LVladymyr/WAFEL-Evaluation-Board/Documents/2_Architecture/Шини живлення.md

Розробка плати захисту батареї (BMS), здатної витримати струм 20 А, вимагає ретельного підходу на всіх етапах — від вибору компонентів до тестування. Ось покрокова інструкція, яка допоможе вам досягти цієї мети.

1️⃣ Вибір ключових компонентів

Основа надійної BMS — це силова частина, розрахована з великим запасом міцності.

· Силові транзистори (MOSFET): Це найкритичніший елемент. Обирайте польові транзистори з допустимим струмом щонайменше 40-50 А (запас у 2-2.5 рази). Звертайте увагу на параметр R_{DS(on)} — чим він менший, тим менше буде нагрівання.
· Струмовимірювальний шунт: Номінальна потужність резистора (шунта) повинна бути розрахована на тривале проходження 20 А. Використовуйте формулу P = I^2 \times R. Наприклад, для шунта 1 мОм потужність розсіювання становитиме 20^2 \times 0.001 = 0.4 Вт, тому варто використовувати резистор на 1 Вт і більше.
· Друкована плата (PCB): Для струму 20 А стандартна доріжка завтовшки 1 oz (35 мкм) завширшки повинна бути не менше 12-15 мм. Значно краще:
  · Використовувати товщину міді 2 oz (70 мкм) або більше.
  · Видалити паяльну маску з силових доріжок та посилити їх шаром припою.
  · Використовувати багатошарову плату з дублюванням доріжок у внутрішніх шарах через велику кількість перехідних отворів (via).

2️⃣ Терморозрахунок та тепловідведення

Струм 20 А неминуче спричинить нагрівання, навіть на якісних компонентах. Ігнорування цього етапу призводить до деградації акумулятора або виходу BMS з ладу.

· Розрахунок втрат: Оцініть тепловиділення на ключах: P_{потерь} = I^2 \times R_{DS(on)}. Якщо R_{DS(on)} дорівнює 5 мОм, а струм 20 А, потужність становитиме 2 Вт. Це значна величина для одного корпусу.
· Радіатор: Для MOSFET у корпусах типу TO-220 або D2PAK обов'язково використовуйте радіатор. Для планарних компонентів використовуйте полігони міді великої площі на обох сторонах плати, з'єднані теплопровідними перехідними отворами.
· Температурний контроль: Під час роботи температура найгарячішої точки (кристалу MOSFET) не повинна перевищувати 80-100°C (залежно від даташиту).

3️⃣ Тестування та верифікація

Теоретичних розрахунків недостатньо. Фізичне тестування — єдиний спосіб гарантувати надійність. Насамперед зверніть увагу на теплові випробування, оскільки саме перегрів є основною причиною виходу BMS з ладу .

Обов'язкові види тестів:

Тип тесту Мета Інструмент
Тривале навантаження Перевірка здатності витримувати 20 А протягом 30-60 хвилин без відключення. Електронне навантаження, акумулятор або потужний джерело живлення.
Тепловізійний контроль Виявлення "гарячих точок" на платі та перевірка ефективності відведення тепла . Тепловізор або безконтактний термометр (пірометр).
Тест захисту (Overcurrent) Перевірка спрацьовування захисту при струмі трохи вище 20 А (наприклад, 22-25 А). Електронне навантаження, осцилограф (для вимірювання часу спрацьовування).

4️⃣ Додаткові критерії якості

· Силові роз'єми: Використовуйте роз'єми, розраховані на струм 30 А і більше (наприклад, клемники на гвинтах, роз'єми XT60/XT90). Контакти мають бути мідними, з покриттям, що запобігає окисленню.
· Калібрування: Якщо плата використовує мікроконтролер із вимірюванням струму, обов'язково відкалібруйте шунт за допомогою еталонного навантаження, щоб відсічка за струмом відбувалася точно при заданому значенні.

Висновок: Щоб впевнитись у надійності, вам потрібно закласти двократний запас міцності за струмом для MOSFET, забезпечити широкі мідні доріжки (2 oz) або шини, а потім провести тепловізійне тестування під навантаженням 20 А в найгірших умовах експлуатації (наприклад, у закритому корпусі). Якщо після 30 хвилин роботи температура компонентів стабілізувалася в межах допустимих значень, плату можна вважати придатною.

Чи плануєте ви використовувати готовий мікросхемний контролер (наприклад, TI BQ769x0) або будувати схему на дискретних компонентах? Від цього залежать нюанси налаштування струмового захисту.

Питання слушне. Посилення доріжок додатковою міддю (часто це називають solder jumper, bus bar або просто stripping) — це один з найефективніших і найпоширеніших методів у промисловому та хобійному дизайні BMS для струмів від 15-20 А і вище.

Відповідь коротко: Це не просто критично, часто це єдиний спосіб уникнути перегріву плати без переходу на багатошарову плату з товстою міддю (3+ oz).

Однак, цей метод має нюанси. Якщо зробити це неправильно, ви не лише не посилите плату, але й створите ризик короткого замикання або відшарування доріжок. Ось детальний розбір:

1️⃣ Чому стандартних доріжок недостатньо для 20 А?

Давайте порахуємо. Для зовнішнього шару при підвищенні температури на 20°C:

· Мідь 1 oz (35 мкм): Щоб безпечно провести 20 А, потрібна доріжка шириною від 12 до 15 мм.
· Мідь 2 oz (70 мкм): Потрібна ширина близько 6-8 мм.

Якщо ваша BMS компактна (а BMS зазвичай намагаються зробити якомога меншими, щоб влізти в корпус акумулятора), фізично розмістити доріжки такої ширини на платі неможливо. Саме тут на допомогу приходить додатковий шар припою або міді поверх доріжки.

2️⃣ Як правильно посилювати (Технологія)

Існує два принципово різних підходи:

А. Покриття доріжок шаром припою (Tin/Lead)

Це найпростіший метод для ручного складання або дрібносерійного виробництва.

· Як робиться: На етапі проєктування ви знімаєте паяльну маску (solder mask) з силової доріжки. Після пайки компонентів ви вручну або хвилею припою наносите товстий шар припою на відкриту мідь.
· Фізика: Питомий опір припою (олово-свинець або безсвинцевий) приблизно в 5-10 разів вищий, ніж у міді. Тому сам по собі шар припою проводить струм набагато гірше за мідь.
· Чому це працює: Припій діє як тепловідвід (радіатор). Він не стільки зменшує падіння напруги, скільки акумулює тепло і збільшує площу поверхні для розсіювання тепла, не даючи мідній доріжці перегрітися і відшаруватися від текстоліту.
· Недолік: Припій не має механічної міцності. При сильному нагріванні (наприклад, при короткому замиканні) він може попливти.

Б. Пайка мідної шини (Bus bar) або товстого дроту

Це професійний підхід для струмів 20 А+, особливо якщо плата працює в умовах високої температури навколишнього середовища.

· Як робиться: Поверх силової доріжки (через отвори в масці) припаюється мідний дріт калібру AWG 12-14 (2.5-4 мм²) або спеціально вигнута мідна шинка.
· Перевага: Мідь має відмінну провідність. Це реально знижує опір шляху, а не просто розподіляє тепло.
· Важливо: Шинка повинна бути припаяна по всій довжині силової доріжки, а не тільки в точках входу/виходу. Інакше струм піде через припій, а не через шинку.

3️⃣ Ризики, якщо зробити це неправильно

Якщо ви просто відкриєте маску і наллєте "гірку" припою на тонку доріжку (1 oz), ви можете зіткнутися з проблемами:

1. Термомеханічне руйнування: Мідь (1 oz) дуже тонка. При нагріванні струмом коефіцієнт розширення міді та текстоліту відрізняється. Якщо зверху налито товстий шар припою, який має власне теплове розширення, доріжка може просто відірватися від основи (здуття або відшарування).
2. Падіння напруги (IR Drop): Якщо ви залишили довгу тонку доріжку (наприклад, 2 мм) і просто залили її припоєм, основний опір все одно визначатиметься перетином міді (яка залишилася тонкою), а не припою. Ви отримаєте помилку спрацьовування захисту від перенапруги на шунті через паразитний опір.
3. Крихкість: Надлишок припою може тріскатися при вібрації.

4️⃣ Рекомендація для надійної роботи при 20 А

Якщо ви хочете бути впевнені на 100%, дотримуйтесь комбінованого підходу:

1. Закажіть плату з товщиною міді 2 oz (70 мкм). Різниця в ціні між 1 oz і 2 oz для невеликої плати BMS мізерна, але це дає базову міцність.
2. Проєктуйте силові доріжки шириною не менше 5-7 мм (з урахуванням 2 oz).
3. Видаліть маску на всій довжині цих доріжок.
4. Поверх доріжок нанесіть товстий шар припою (лудіння), використовуючи паяльник з широким жалом (типу "лопатка") або хвилю припою.
5. Опціонально для критичних місць: У місцях підключення проводів (P+, B+, P-, B-) встановіть мідні клеми (наскрізні люверси) або припаяйте тонку мідну шинку.

Висновок

Посилення міддю (припоєм) є критично необхідним, якщо ваша плата має компактні розміри, або ви використовуєте стандартну товщину міді 1 oz.

Однак, це не повинно бути єдиним методом. Найкраща практика для 20 А:

· Заводський метод: Замовити плату з товщиною міді 2-3 oz (70-105 мкм) без маски на силових доріжках, щоб завод наніс товстий шар гальванічного припою (HASL або ENIG з посиленням).
· DIY метод: Взяти плату 2 oz, відкрити маску і "наростити" доріжки припоєм, контролюючи, щоб не перегріти мідь (використовувати флюс і потужний паяльник швидко).

Якщо ви залишите тонкі доріжки (1 oz, 2-3 мм) без посилення, плата або вийде з ладу через перегрів на 20 А, або буде створювати значне падіння напруги, що призведе до помилкового спрацьовування захисту BMS.

Ви абсолютно праві, вимагати прорахунок — це коректно. Давайте розберемо це не на рівні "досвід каже", а на рівні цифр, фізики та інженерної методології.

Я наведу розрахунок для найгіршого сценарію (worst-case), який зазвичай використовують у промисловому дизайні.

1️⃣ Вихідні дані для розрахунку

Припустимо, ми маємо плату BMS, де силова доріжка має довжину 50 мм (це типова відстань від виводу MOSFET до клеми).

Параметри:

· Струм (I): 20 А
· Товщина міді: 2 oz (70 мкм = 7 \times 10^{-5} м)
· Ширина доріжки (w): 6 мм = 0.006 м
· Питомий опір міді (\rho): 1.68 \times 10^{-8} \, \Omega \cdot \text{м} (при 20°C)
· Температурний коефіцієнт опору міді (\alpha): 0.0039 \text{°C}^{-1}

---

2️⃣ Розрахунок опору самої мідної доріжки (без припою)

Площа перерізу міді:

S = \text{товщина} \times \text{ширина} = (70 \times 10^{-6}) \times 0.006 = 4.2 \times 10^{-7} \, \text{м}^2

Опір доріжки при 20°C:

R_{\text{мідь,20°C}} = \rho \times \frac{L}{S} = 1.68 \times 10^{-8} \times \frac{0.05}{4.2 \times 10^{-7}} \approx 0.002 \, \Omega = 2 \, \text{мОм}

Втрати потужності на мідній доріжці (при 20°C):

P_{\text{мідь}} = I^2 \times R = 20^2 \times 0.002 = 0.8 \, \text{Вт}

Нагрів доріжки:
0.8 Вт на відрізку 50 мм для доріжки 6 мм — це дуже мала потужність. За стандартами IPC-2221, при такій потужності підвищення температури доріжки відносно навколишнього середовища становитиме менше 10–15°C, що є безпечним.

Але це ще не вся історія.

---

3️⃣ Чому 2 мОм — це мало, але важливо врахувати нагрів

При робочій температурі, скажімо, 60°C (нагрів від MOSFET, акумулятора або навколишнього середовища), опір зростає:

R_{\text{мідь,60°C}} = R_{20°C} \times \left(1 + \alpha \times (60 - 20)\right) = 0.002 \times (1 + 0.0039 \times 40) \approx 0.002312 \, \Omega

Втрати зростають до:

P_{\text{мідь,60°C}} = 400 \times 0.002312 \approx 0.925 \, \text{Вт}

Це все ще прийнятно. Чисто мідний провідник 6 мм при 2 oz вже здатний витримати 20 А з точки зору нагріву.

---

4️⃣ Навіщо тоді потрібен гальванічний припій (або відкрита маска)?

Тут ключове — не зменшення опору міді, а зниження температури в зонах концентрації струму та забезпечення довготривалої надійності.

Є два фактори, які руйнують тонкі доріжки при 20 А:

А. Перехідні опори на з'єднаннях

Найгарячіша точка на платі — це не середина доріжки, а місця:

· пайки виводів MOSFET до доріжки;
· підключення силових проводів (B+, P+).

У цих точках через нерівномірність пайки або механічні навантаження може виникати локальний опір навіть у кілька мОм. При 20 А це дає додаткові вати тепла в точці площею в кілька квадратних міліметрів.

Відкрита маска + товстий шар гальванічного припою дозволяють:

· збільшити теплову масу в цих критичних зонах;
· вирівняти температуру по всій довжині доріжки;
· уникнути локального перегріву, який може призвести до відшарування доріжки.

Б. Циклічні навантаження (теплові удари)

Якщо BMS працює в імпульсному режимі (наприклад, електроінструмент, дрон, стартер), доріжка постійно нагрівається і охолоджується.

· Без гальванічного припою: тонка доріжка (навіть 2 oz) зазнає мікродеформацій. З часом (сотні циклів) можливе відшарування від діелектрика.
· З гальванічним припоєм: товстий шар припою (який зазвичай становить 20–50 мкм поверх міді) працює як демпфер і додатковий провідник тепла, зменшуючи амплітуду температурних коливань у самій міді.

---

5️⃣ Чому я обрав саме 5–7 мм при 2 oz?

Це діапазон, який дає інженерний запас з урахуванням трьох факторів:

1. Технологічність виробництва:
   При ширині менше 5 мм для 2 oz різко зростає ризик недотравлення (undercut) при хімічному травленні — доріжка може вийти фактично тоншою, ніж розраховано.
2. Падіння напруги на BMS:
   Для BMS важливо, щоб падіння напруги на силовій частині було мінімальним, інакше:
   · збільшується похибка вимірювання струму (якщо використовується шунт);
   · зростає ймовірність помилкового спрацьовування захисту при різких кидках струму.
   Падіння напруги на доріжці \Delta U = I \times R:
   \Delta U = 20 \times 0.002 = 0.04 \, \text{В} = 40 \, \text{мВ}

   Це прийнятно. Якщо ж доріжка буде 3 мм при 1 oz, R зросте до 8–10 мОм, а падіння — до 160–200 мВ, що вже суттєво впливає на роботу схеми вимірювання.
3. Сумісність з гальванічним покриттям:
   При ширині менше 5 мм нанесення товстого шару гальванічного припою технологічно складніше через ризик утворення "грибків" (нерівномірного наростання), що може призвести до коротких замикань між сусідніми доріжками.

---

6️⃣ Підсумковий прорахунок надійності

Параметр Без посилення (1 oz, 3 мм) З посиленням (2 oz + припій, 6 мм)
Опір доріжки (20°C) ~8–10 мОм ~2 мОм
Втрати потужності ~3.2–4 Вт ~0.8 Вт
Підвищення температури ~40–60°C (ризик відшарування) ~10–15°C
Падіння напруги 160–200 мВ 40 мВ
Стійкість до вібрації/циклів Низька Висока

Висновок:
Я вважаю 5–7 мм при 2 oz з гальванічним припоєм достатнім не тому, що "так роблять", а тому що це дає:

· опір < 2.5 мОм на типових довжинах;
· тепловиділення < 1 Вт, що не потребує примусового охолодження;
· технологічний запас на нерівномірність травлення та пайки;
· сумісність зі стандартними техпроцесами виробництва PCB.

Якщо ж плата працюватиме в замкнутому корпусі без вентиляції за температури навколишнього середовища вище 50°C, я б рекомендував збільшити ширину до 10–12 мм або використовувати 3 oz міді з тією ж шириною 5–7 мм.
Це класичний інженерний виклик: обмежений простір + високий струм + замкнутий корпус = мідна шина (bus bar) як єдине правильне рішення.

Давайте розберемо, як інтегрувати шину в плату BMS так, щоб це було технологічно, надійно і не "з'їло" весь корисний простір.

---

1️⃣ Концепція: шина як несучий елемент

У компактних BMS для високих струмів (електроінструмент, e-bike, дрони, стартерні батареї) класичний підхід змінюється:

Традиційний підхід Підхід з шиною
Весь струм іде через доріжки PCB PCB несе лише сигнали та слабкострумові ланцюги
MOSFET припаяні до PCB MOSFET припаяні до шини, PCB "висить" на шині
Тепло розсіюється через мідні полігони Шина працює як радіатор і струмопровід

Ключова ідея: ви робите PCB сигнальною (товщина 1–1.6 мм, 1–2 oz), а силову комутацію виносите на окрему мідну шину, яка механічно з'єднана з платою.

---

2️⃣ Архітектура плати з шиною

Існує три основних способи інтеграції:

Варіант А: Шина поверх PCB (найпростіший для прототипу)

Шина виготовляється з мідної смуги товщиною 1.5–2 мм, шириною 8–12 мм (залежить від струму та місця). Вона припаюється поверх силових доріжок PCB по всій довжині.

Як реалізувати:

1. На PCB проєктуєте силові доріжки шириною 5–7 мм (2 oz) із відкритою маскою.
2. Замовляєте або вирізаєте мідні шини за формою траси.
3. Встановлюєте MOSFET так, щоб їхні дрейни/витоки контактували безпосередньо з шиною (часто через паз у шині або вертикальне розташування).
4. Шина припаюється до PCB по всій довжині потужним паяльником або на грілці.

Переваги: простота, можна зробити вручну.
Недоліки: збільшує загальну висоту плати, шина займає місце поверх компонентів.

Варіант Б: Шина як окремий шар (професійний)

PCB проєктується як двошаровка або багатошаровка, де один із шарів (зазвичай верхній або нижній) повністю замінений на товсту мідну шину, що вставляється в плату як вставка.

Як реалізувати:

1. У PCB вирізається фрезероване вікно (cavity) за формою шини.
2. Шина вставляється у вікно і фіксується на рівні поверхні плати.
3. Виводи MOSFET падаються безпосередньо на шину через отвори в PCB (відстань між шиною та виводом мінімальна).

Переваги: мінімальна висота, найкраще охолодження.
Недоліки: висока вартість виробництва, потребує замовлення PCB з фрезеруванням під шину.

Варіант В: Гібридний (рекомендований для 20 А)

Комбінація: товста мідь PCB (3–4 oz) + накладні шини лише в критичних точках (підключення акумулятора, MOSFET, шунт).

Як реалізувати:

1. Замовляєте PCB з товщиною міді 3 oz (105 мкм) на силових шарах.
2. У місцях підключення проводів (B+, B-, P+, P-) і під MOSFET встановлюєте мідні накладки (bus bar pads) товщиною 1 мм, які припаюються до PCB.
3. Ці накладки з'єднуються між собою короткими перемичками або безпосередньо виводами компонентів.

---

3️⃣ Як правильно з'єднати шину з PCB

Найслабше місце — це перехід між шиною та PCB. При 20 А навіть 1 мОм додаткового опору дасть 0.4 Вт тепла в точці.

Методи з'єднання (від надійнішого до менш надійного):

Метод Опис Коли використовувати
Гвинтове з'єднання + пайка Шина притискається гвинтами через ізольовані втулки до PCB, додатково пропаюється Промислові вироби, вібраційні навантаження
Наскрізна пайка (THT) Шина має "ніжки", які вставляються в отвори PCB і падаються з обох боків Найкраще для компактних конструкцій
SMT-пайка великої площі Шина припаюється до відкритої мідної зони на PCB через товстий шар припою Прототипи, низька вібрація
Провідникові перемички Замість шини — кілька паралельних дротів AWG 12–14 Коли немає можливості виготовити шину

Для 20 А я рекомендую:
Шина товщиною 1–1.5 мм з наскрізними отворами під пайку (4–6 отворів діаметром 1.5–2 мм на кожне з'єднання), що забезпечує механічну фіксацію та низький перехідний опір.

---

4️⃣ Терморозрахунок шини в замкнутому просторі

У замкнутому корпусі немає конвекції, тому нагрів визначається лише теплоємністю маси міді та теплопередачею через корпус.

Розрахунок для шини 1.5×10×50 мм (об'єм 750 мм³):

Маса міді:

m = \rho_{\text{Cu}} \times V = 8.96 \, \text{г/см}^3 \times 0.75 \, \text{см}^3 \approx 6.7 \, \text{г}

Теплоємність міді: C_{\text{Cu}} \approx 0.385 \, \text{Дж/(г·°C)}

Теплоємність шини:

C_{\text{шина}} = 6.7 \times 0.385 \approx 2.6 \, \text{Дж/°C}

Це означає, що при потужності втрат 1 Вт (реалістичне значення для шини + MOSFET при 20 А) шина нагріватиметься зі швидкістю:

\frac{dT}{dt} = \frac{P}{C} = \frac{1}{2.6} \approx 0.38 \, \text{°C/с}

Тобто за 30 секунд — підйом на ~11°C, за 5 хвилин — вихід на теплову рівновагу з корпусом.

Важливо: у замкнутому просторі шина має бути термічно з'єднана з корпусом (через теплопровідну прокладку або безпосередній контакт), інакше температура всередині може перевищити 80–90°C навіть при 20 А.

---

5️⃣ Практична послідовність проєктування

Якщо у вас жорсткі вимоги до розміру та замкнутий корпус, ось покрокова інструкція:

Крок 1. Визначте, де будуть шини

Зазвичай потрібні 3–4 шини:

· B- / P- (шлях струму через MOSFET)
· B+ / P+ (прямий шлях, часто через шунт)

Крок 2. Спроєктуйте PCB із "кишенями" під шини

· Зробіть у PCB фрезеровані вирізи (slots) або наскрізні отвори для фіксації шин.
· На місцях пайки шин відкрийте маску та зробіть тепловідвідні via (масив отворів діаметром 0.3–0.5 мм для передачі тепла на інший бік).

Крок 3. Виготовте шини

· Матеріал: C11000 (електролітична мідь), товщина 1–1.5 мм.
· Форма: прямокутна або Г-подібна (якщо потрібно обійти компоненти).
· Поверхня: краще лудіння (Sn) або сріблення для легкості пайки та захисту від окислення.

Крок 4. Зберіть у правильному порядку

1. Спочатку припаяйте шини до PCB (використовуйте потужний паяльник 80–100 Вт або нагрівальну плиту).
2. Потім встановіть MOSFET безпосередньо на шини (часто з використанням SMD-пайки через отвори в PCB або вертикального монтажу).
3. Потім — слабкострумову частину (мікроконтролер, драйвери, резистори).

Крок 5. Термоінтерфейс із корпусом

Якщо корпус металевий або має радіатор:

· Використовуйте керамічні термопрокладки (0.5–1 мм) між шиною та корпусом.
· Якщо корпус пластиковий — передбачте вентиляційні отвори або збільште масу шини (2 мм замість 1.5).

---

6️⃣ Перевірка: що контролювати після складання

Після інтеграції шини обов'язково перевірте:

1. Опір силового тракту: виміряйте мікроомметром або методом падіння напруги (20 А через навантаження, виміряйте між B- та P-). Норма — < 5 мОм (включаючи MOSFET).
2. Температуру під навантаженням: тепловізором після 10 хвилин роботи в замкнутому корпусі. Максимум — < 80°C на шині біля MOSFET.
3. Відсутність механічного люфту: шина не повинна рухатися відносно PCB після пайки. Якщо є — додайте гвинтову фіксацію.

---

Висновок

Для ваших умов (замкнутий простір + обмежений розмір + 20 А) оптимальне рішення:

PCB з товщиною міді 2–3 oz + окремі мідні шини (1–1.5 мм) у місцях силової комутації, з'єднані з PCB через наскрізну пайку та додатково термічно зв'язані з корпусом.

Це дає:

· Мінімальний опір (< 2–3 мОм)
· Ефективне тепловідведення (маса міді працює як теплоакумулятор)
· Компактність (шини можна розташувати вертикально або обійти компоненти)
· Механічну надійність

Якщо ви маєте конкретний ескіз плати або орієнтовні габарити, можу допомогти з розміщенням шин і розрахунком перерізу.
Коротка відповідь: Так, можна і це поширена практика. Але є критичні нюанси: паяти шину для зміни форми можна лише до її встановлення на плату, і це потребує дотримання технології, щоб не створити "холодних спаїв" у силовому тракті.

Давайте розберемо, як правильно зробити складну шину, коли прямими відрізками не обійтися.

---

1️⃣ Чому не можна просто "перетнути" лінії на PCB?

Коли ви маєте кілька MOSFET (наприклад, 4–6 штук у паралель для зменшення R_{DS(on)}), виникає типова проблема:

· Дрейни (або витоки) групи MOSFET мають бути об'єднані в одну шину.
· Витоки (або дрейни) — в іншу.
· Ці дві шини не повинні перетинатися ні на PCB, ні в повітрі.

На звичайній PCB довелося б робити обхідні маршрути, що збільшує довжину шляху струму, додає паразитну індуктивність і створює "гарячі точки". Мідна шина вирішує це тим, що може мати складну 3D-форму, обходячи одна одну в різних площинах.

---

2️⃣ Технології формування складної шини

Існує три способи отримати шину складної форми, які відрізняються надійністю та складністю:

Варіант 1: Механічне згинання (рекомендований)

Це коли ви берете пряму мідну смугу і згинаєте її в потрібну форму без паяння.

Як робити:

· Матеріал: м'яка (відпалена) мідь товщиною 1–1.5 мм. Hard-drawn мідь буде тріскатися на згинах.
· Радіус згину: не менше 2–3 товщин матеріалу (для 1.5 мм — радіус від 3 мм).
· Інструмент: лещата з м'якими губками, спеціальний гнучкий верстат або акуратно молотком через оправку.

Переваги: монолітна шина без додаткових з'єднань, мінімальний опір, максимальна надійність.
Недоліки: складно зробити складну 3D-форму з кількома вигинами в різних площинах.

Варіант 2: Паяння окремих сегментів (ваш випадок)

Коли форма надто складна для згинання (наприклад, потрібно обійти компонент з усіх боків або зробити "місток" над іншою шиною), сегменти з'єднуються паянням.

Правила паяння шин:

1. З'єднання внахлест (lap joint), а не встик. Мінімальна довжина нахлесту — 10–15 мм для 20 А.
2. Площа контакту має бути достатньою, щоб перехідний опір був < 0.1 мОм. Орієнтовно: для шини 10×1.5 мм площа нахлесту має бути не менше 100 мм² (тобто 10×10 мм).
3. Фіксація: перед паянням сегменти треба зафіксувати струбциною або скруткою — під час нагрівання мідь "грає", і з'єднання може зміститися.
4. Температура: потужний паяльник (100+ Вт) або газова пальник з тонким наконечником. Мідь швидко відводить тепло — звичайним паяльником 40 Вт ви просто не прогрієте місце з'єднання до потрібної температури.

Критично: паяти шину після встановлення на плату для зміни її форми — погана ідея. Ви ризикуєте:

· перегріти та відшарувати доріжки PCB;
· розплавити сусідні пластикові корпуси компонентів;
· отримати ненадійне з'єднання через неможливість якісно прогріти масивну мідь.

Варіант 3: Гвинтове з'єднання сегментів

Альтернатива паянню для складних форм — з'єднання сегментів через гвинти (M3 або M4) з шайбами.

Переваги: розбірність, відсутність термічного впливу на PCB.
Недоліки: більший перехідний опір, якщо не використовувати спеціальні мідні шайби та антиоксидантну пасту.

---

3️⃣ Як спроєктувати складну шину для кількох MOSFET

Ось типова конфігурація для BMS з 4–6 MOSFET у паралель, яка потребує складної форми шини:

Конструктивне рішення: дворівнева шина

Одна шина (наприклад, спільний витік) розташовується нижче, безпосередньо на PCB, друга (спільний дрейни) — вище, у вигляді "містка".

Як це реалізувати паянням сегментів:

1. Нижня шина: пряма мідна смуга, що проходить під виводами MOSFET. Вона паяється до PCB через наскрізні отвори.
2. Верхня шина: складається з трьох сегментів:
   · Два вертикальних стояка, припаяних до нижньої шини або безпосередньо до PCB.
   · Один горизонтальний сегмент, що з'єднує стояки зверху, утворюючи арку над компонентами.
3. Місця паяння сегментів: розташовуються над рівнем компонентів, щоб калюжі припою не капали на плату.

Важливий нюанс: термічний зв'язок

Якщо ви паяєте сегменти шини, місце паяння стає термічним опором. У точці з'єднання буде трохи вища температура, ніж у монолітній шині.

Для 20 А це не критично, якщо:

· площа нахлесту ≥ 100 мм²;
· з'єднання виконано якісним товстошаровим припоєм (наприклад, Sn96.5Ag3Cu0.5 — SAC305);
· кількість з'єднань на одному силовому шляху не перевищує 2–3.

---

4️⃣ Альтернатива: багатошарова шина з ізоляцією

Якщо вам потрібно перетнути дві силові лінії (наприклад, B- і P+), але вони не можуть фізично розминутися, рішення — рознести їх у різних площинах з ізоляцією між ними.

Конструкція:

· Нижня шина (товщина 1.5 мм) лежить на PCB.
· Поверх неї — шар ізоляції (поліімідна стрічка Kapton, склотекстоліт 0.5 мм або термозбіжна трубка).
· Верхня шина (товщина 1.5 мм) проходить над ізоляцією, перетинаючи нижню.

Таке рішення часто використовується в промислових BMS для електроінструменту, де щільність монтажу максимальна.

---

5️⃣ Практичні рекомендації для вашого випадку

1. Розділіть завдання:
   · Визначте, які MOSFET комутують заряд, які — розряд (якщо це окремі групи).
   · Спробуйте згрупувати MOSFET так, щоб шини були максимально прямими, а складні форми знадобилися лише в 1–2 місцях.
2. Використовуйте комбінацію:
   · Основні магістралі зробіть із цілісних зігнутих шин.
   · Для перетинів або обходу компонентів додайте припаяні сегменти внахлест.
3. Контролюйте порядок складання:
   · Спочатку сформуйте та (за потреби) спаяйте між собою всі сегменти шини поза платою.
   · Потім встановіть готову збірну шину на PCB і припаяйте її до контактних майданчиків одним етапом.
   · Після цього встановлюйте MOSFET — їхні виводи мають лягти на шину без натягу.
4. Не економте на припої та флюсі:
   · Для паяння шин між собою використовуйте активний флюс (наприклад, на основі каніфолі з додаванням гліцерину) або паяльну пасту.
   · Після паяння обов'язково відмийте залишки флюсу — вони можуть спричинити корозію або витік струму між шинами.

---

Висновок

Паяти шину для зміни форми можна і потрібно, якщо пряма шина не дозволяє обійти компоненти або розвести силові лінії. Головні правила:

· Паяйте поза платою, збираючи шину як окремий вузол.
· Використовуйте з'єднання внахлест із площею ≥ 100 мм².
· Кількість паяних з'єднань на одному струмовому шляху — не більше 2–3.
· Після складання перевірте тепловізором саме місця паяних стиків — вони будуть нагріватися сильніше за цілісну мідь.

Якщо ви маєте конкретну схему розташування MOSFET і орієнтовні габарити плати, можу допомогти спроєктувати форму шини з мінімальною кількістю паяних з'єднань.

Це ключове питання для надійної BMS. З'єднання MOSFET і діодів із шиною — це те місце, де найчастіше виникають проблеми: перегрів, підвищений опір, механічні поломки. Давайте розберемо всі варіанти від найкращого до прийнятного.

---

1️⃣ Загальний принцип

Для струму 20 А в замкнутому просторі кожен силовий вивід MOSFET або діода має бути безпосередньо з'єднаний із шиною, а не через тонку доріжку PCB.

Основні способи:

Спосіб Надійність Складність Застосування
Притиск через ізольовану прокладку ⭐⭐⭐⭐⭐ Висока Промислові BMS, IGBT модулі
Пайка виводом на шину (THT) ⭐⭐⭐⭐ Середня Найпоширеніший для BMS
SMD-компоненти на шині ⭐⭐⭐ Висока Для компактних плат
Через PCB з товстими доріжками ⭐⭐ Низька Для струмів < 15 А

Я рекомендую пайку виводом на шину — це оптимальне поєднання надійності, технологічності та ремонтопридатності.

---

2️⃣ Типи корпусів MOSFET та їх з'єднання з шиною

А. Корпус TO-220 (найпоширеніший для BMS)

TO-220 має металевий тепловідвід (таб), який електрично з'єднаний з дрейном (для N-канальних MOSFET, які зазвичай використовуються в BMS).

Варіанти з'єднання:

Варіант 1: Вертикальний монтаж із пайкою виводів до шини

```
         MOSFET TO-220
         ┌─────────┐
         │         │
    ┌────┤  таб    │
    │    │ (дрейн) │
    │    └─────────┘
    │     │ │ │
    │     │ │ └─── виток (source) — до шини P-
    │     │ └───── затвор (gate) — до драйвера
    │     └─────── виток (source) — до шини P-
    │
    └───── мідна шина (дрейн)
```

Реалізація:

1. Шина для дрейнів виготовляється з виступами (пелюстками) у місцях розташування MOSFET.
2. Виводи MOSFET вставляються в отвори PCB (яка розташована над або під шиною).
3. Таб (металева спинка) припаюється безпосередньо до шини по всій площі контакту.

Технологія пайки табу до шини:

· Використовуйте потужний паяльник (80–100 Вт) або нагрівальну плиту.
· Нанесіть флюс на обидві поверхні.
· Припій — товстошаровий (SAC305 або аналог).
· Важливо: таб MOSFET не можна перегрівати > 260°C більше 10 секунд. Використовуйте радіаторний затискач на корпусі під час пайки.

Варіант 2: Горизонтальний (лежачий) монтаж

Для зменшення висоти конструкції.

```
         шина (дрейн)
    ┌─────────────────────┐
    │                     │
    │   ┌─────────┐       │
    │   │ MOSFET  │       │
    │   │  TO-220 │       │
    │   └────┬────┘       │
    │        │            │
    │   виводи (source, gate)
    │        │
    └────────┼────────────┘
           PCB
```

Особливості:

· Таб припаюється до шини збоку або знизу.
· Виводи загинаються під прямим кутом і вставляються в PCB.
· Потребує точного виготовлення шини з пазами під корпус.

---

Б. Корпус D2PAK (TO-263) — SMD-варіант

Для максимальної компактності.

З'єднання:

· Великий тепловідвід (таб) — це також вивід дрейну.
· Таб припаюється безпосередньо до мідної зони на PCB, яка з'єднана з шиною через масив перехідних отворів (via) або є частиною шини.

Для 20 А: рекомендую використовувати не менше 2–3 паралельних D2PAK для зменшення теплового навантаження на один корпус.

---

В. Корпус TO-247 (для потужних BMS)

Якщо використовуєте великі MOSFET (наприклад, для зниження R_{DS(on)}):

· Таб також є дрейном.
· Виводи товщі, потребують отворів у PCB діаметром 1.5–2 мм.
· Рекомендація: використовувати гвинтове кріплення табу до шини через ізольовану прокладку (якщо потрібна гальванічна розв'язка) або безпосередньо (якщо спільний потенціал).

---

3️⃣ З'єднання силових діодів (Шотткі)

Діоди використовуються для:

· Захисту від зворотної полярності
· Зворотного струму при паралельній роботі BMS
· Снабберних ланцюгів (хоча там струми малі)

Для струму 20 А:

Тип корпусу Спосіб з'єднання
TO-220 Аналогічно MOSFET: катод (таб) на шину, анод — через PCB або окремий провід.
DPAK / D2PAK SMD-пайка на мідну зону, з'єднану з шиною.
DO-201 (дискретний) Не підходить для 20 А — занадто малий переріз виводів.

Важливо: діоди гріються значно більше, ніж MOSFET при однаковому струмі (падіння напруги 0.4–0.6 В проти 0.01–0.02 В у MOSFET). Тому для 20 А діод має бути розрахований на 25–30 А і мати хороший тепловий контакт із шиною/корпусом.

---

4️⃣ Конструктивне рішення: PCB як "міст" між компонентами та шиною

Найпрактичніший підхід для вашого випадку (20 А, кілька MOSFET, замкнутий простір):

Структура з трьома рівнями

```
    Рівень 3:   Шина 2 (source) ─────┬─────
                                       │
    Рівень 2:   PCB (сигнали, драйвери) │
                    │ │ │               │
    Рівень 1:   Шина 1 (drain) ────────┴─────
                    │
               MOSFET (вертикально)
```

Як це реалізувати:

1. Нижня шина (дрейн): товста мідь (1–1.5 мм) з отворами під виводи MOSFET або з майданчиками для пайки табу.
2. PCB: розташовується над нижньою шиною на стійках (висота 5–8 мм). У PCB є отвори для виводів MOSFET та діодів.
3. Верхня шина (витік): якщо потрібна окрема шина для витоків — розташовується над PCB на ізоляторах.

Переваги:

· PCB не несе силового струму — тільки сигнали.
· MOSFET мають мінімальний шлях струму.
· Відмінне охолодження (шини працюють як радіатори).
· Легко замінити MOSFET у разі виходу з ладу.

---

5️⃣ Покрокова інструкція: пайка MOSFET до шини

Необхідне обладнання

· Паяльник 80–100 Вт із широким жалом (типу "лопатка")
· Флюс активний (наприклад, Amtech RMA-223, або спиртоканіфольний)
· Припій Sn60Pb40 або SAC305 (товщина 1–1.5 мм)
· Термозахисний затискач (heat sink clip) на корпус MOSFET
· Спирт для відмивання флюсу

Послідовність

1. Підготовка шини:
   · Зачистіть місце пайки дрібнозернистим наждаком (600–1000).
   · Знежирте спиртом.
   · Нанесіть тонкий шар флюсу.
2. Підготовка MOSFET:
   · Зачистіть таб (якщо є окислення).
   · Надіньте термозахисний затискач на пластиковий корпус (захищає кристал від перегріву).
3. Лудіння:
   · Залудіть шину в місці пайки тонким шаром припою.
   · Залудіть таб MOSFET.
4. Пайка:
   · Встановіть MOSFET на шину, зафіксувавши його (можна використовувати пінцет із фіксатором або тимчасовий затискач).
   · Прогрійте місце з'єднання паяльником до розплавлення припою (260–280°C).
   · Додайте трохи припою, щоб утворився суцільний шар без порожнин.
   · Час нагріву — не більше 5–7 секунд.
5. Контроль:
   · Після остигання перевірте візуально — припій має бути блискучим, без тріщин.
   · Перевірте мультиметром опір між виводом дрейну (табом) та шиною — має бути < 0.5 мОм.
6. Відмивання:
   · Видаліть залишки флюсу спиртом або спеціальним очищувачем.

---

6️⃣ Альтернатива: гвинтове кріплення

Якщо пайка масивних компонентів викликає труднощі, або ви плануєте можливість заміни:

Для TO-220 з гвинтовим отвором у табі:

1. У шині робиться отвір із різьбою M3.
2. Між табом MOSFET і шиною — тонкий шар термопасти (якщо потрібен електричний контакт, використовуйте мідну шайбу).
3. MOSFET притискається гвинтом через ізольовану втулку (якщо таб не повинен мати електричного контакту з шиною).

Недоліки: вищий перехідний опір, потрібен вільний доступ для затягування.

---

7️⃣ Типові помилки та їх уникнення

Помилка Наслідок Рішення
Перегрів MOSFET при пайці Деградація кристала, збільшення R_{DS(on)} Використовуйте термозахисний затискач, паяйте швидко
Недостатня площа контакту табу з шиною Локальний перегрів, відшарування Площа контакту має бути ≥ 50 мм² на 10 А струму
Пайка виводів MOSFET до тонких доріжок PCB Перегрів доріжок, відшарування Виводи паяйте безпосередньо до шини, або використовуйте PCB тільки для сигналів
Використання флюсу, що проводить Витоки струму, корозія Використовуйте каніфольні флюси, після пайки відмивайте
Механічний натяг виводів Тріщини в пайці, відрив Забезпечте, щоб MOSFET стояв без напруження перед пайкою

---

8️⃣ Підсумкова рекомендація для вашого проєкту

Враховуючи:

· 20 А струму
· Замкнутий простір
· Кілька MOSFET (ймовірно, 4–6 у паралель)
· Обмежений розмір

Я рекомендую:

1. Корпус MOSFET: TO-220 (зручність монтажу та заміни) або D2PAK (якщо критична висота).
2. Спосіб з'єднання: пайка табу безпосередньо до мідної шини (товщина 1–1.5 мм) потужним паяльником.
3. Архітектура: нижня шина (дрейн) — суцільна, PCB над нею на стійках, виводи MOSFET проходять через отвори в PCB і паяються до сигнальних доріжок.
4. Термоконтроль: між шиною та корпусом — теплопровідна прокладка, або шина виступає як радіатор.
5. Для діодів: аналогічний підхід, але з урахуванням більшого тепловиділення — можливо, окрема шина або радіатор.

Якщо ви надасте:

· кількість MOSFET (і їх типорозмір),
· орієнтовне компонування на платі,
· чи будуть MOSFET у паралель (і скільки),
