LVladymyr/WAFEL-Evaluation-Board/Documents/Todos.md

Also wrote a task list:
1. Route Current Sense (Connect SRP/SRN pins to main Shunt Resistor with RC filter) 
2. Replace CAN Transceiver (U802: TJA1051T/3) with a Wake-on-CAN capable IC (e.g., TJA1042T/3 or TCAN1042G)
