LVladymyr/WAFEL-Evaluation-Board/Documents/SLUAA09A Translation.md

# Кілька FET разом з моніторами акумуляторів BQ769x2
*Прикладна нотатка (Application Note) — Texas Instruments SLUAA09A*
*Willy Massoth — Вересень 2020 / Переглянуто березень 2022*

---

## Анотація

Типові схеми для сімейства моніторів акумуляторів BQ769x2 (яке включає BQ76952, BQ76942 та BQ769142) показують одиничні послідовні FET з боку високої напруги. Багато розробників потребують паралельного з'єднання FET у своїх конструкціях для підвищення струмової здатності або розсіювання тепла. Цей документ обговорює та демонструє результати комутації кількох FET з використанням пристроїв BQ76952 і надає приклад для розробників, що реалізують кілька FET з цим або іншими пристроями сімейства BQ769x2.

---

## Зміст

1. [Вступ](#1-вступ)
2. [Схема захисту від зворотної зарядки](#2-схема-захисту-від-зворотної-зарядки)
3. [Вибір компонентів захисту від зворотної зарядки](#3-вибір-компонентів-захисту-від-зворотної-зарядки)
4. [Зарядовий насос та ввімкнення FET](#4-зарядовий-насос-та-ввімкнення-fet)
5. [Тестові схеми з паралельними FET](#5-тестові-схеми-з-паралельними-fet)
6. [Драйвер CHG](#6-драйвер-chg)
7. [Шляхи струму драйвера CHG](#7-шляхи-струму-драйвера-chg)
8. [Драйвер DSG](#8-драйвер-dsg)
9. [Шляхи струму драйвера DSG](#9-шляхи-струму-драйвера-dsg)
10. [Висновок](#10-висновок)
11. [Посилання](#11-посилання)
12. [Історія ревізій](#12-історія-ревізій)

---

## 1 Вступ

Типова акумуляторна батарея має один набір клем як для заряду, так і для розряду. Струм проходить через FET заряду та розряду, з'єднані послідовно. Оскільки струм тече через обидва FET, їх розміри і кількість для заряду та розряду однакові. Сімейство моніторів акумуляторів BQ76952, що складається з BQ76942 та BQ76952, підтримує послідовні FET з боку високої напруги. Посилання на BQ76952 у цьому документі, як правило, поширюються на всіх членів сімейства, якщо не зазначено інше. Типова схема з BQ76942 і послідовними FET показана на Рис. 1-1. Схема розрахована на реалізацію з 7 елементами та включає FET попереднього заряду та попереднього розряду. Шлях попереднього заряду використовується для обмеження струму в батарею від зарядного пристрою з фіксованою напругою при глибокому розряді батареї. Шлях попереднього розряду використовується для заряду ємнісних навантажень без стрибка великого струму. При використанні послідовних FET існує можливість заряду через вимкнений FET розряду або розряду через вимкнений FET заряду. Струм через захисний діод вимкненого FET може виробляти значну кількість тепла, тому пристрої BQ76952 використовують функцію захисту тілесного діода для ввімкнення FET, коли струм тече в незахищеному напрямку.

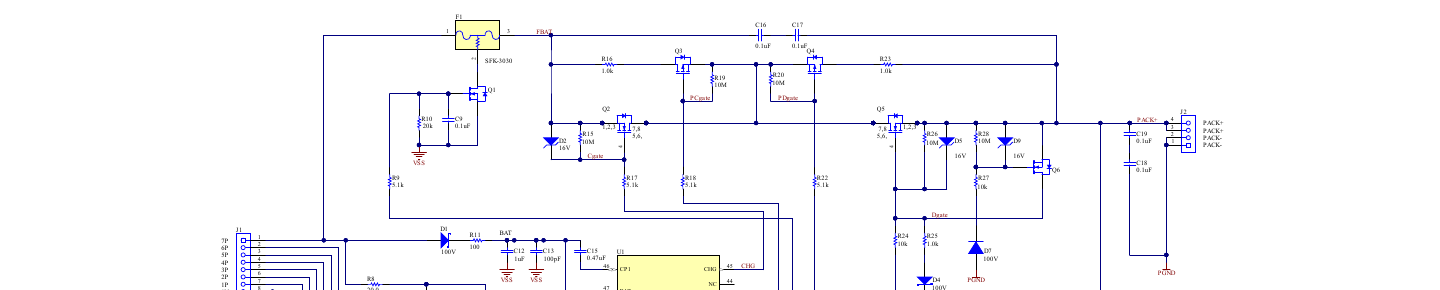
[picture p1: Documents/images/sluaan9a-fig1-1.png]
Рис. 1-1. Типова схема FET послідовної 7S-серії


![[Pasted image 20260403155612.png]]

*Рис. 1-1. Типова схема FET послідовної 7S-серії*

Кількість елементів і конфігурація схеми навколо виводів низької напруги пристрою варіюватимуться залежно від реалізації і, як правило, не будуть показані на подальших схемах у цьому прикладному звіті. Як і основні силові FET, FET попереднього заряду та попереднього розряду мають бути вибрані для конкретної застосунку. Схеми попереднього заряду та попереднього розряду є відносно низькострумовими, щоб уникнути великої потужності в акумуляторному блоці, і не є предметом розгляду цього прикладного звіту.

---

## 2 Схема захисту від зворотної зарядки

Схема включає в себе схему захисту від зворотної зарядки, що складається з Q6 та компонентів, що оточують його затвор. Призначення схеми — утримувати затвор силового FET розряду на потенціалі джерела, щоб тримати його вимкненим, коли клема PACK+ опускається нижче VSS. Ця схема може бути важливою функцією, коли система використовує загальний роз'єм, такий як коаксіальний роз'єм живлення для зарядного пристрою. Оскільки на ринку доступні адаптери обох полярностей, можна підключити неправильний зарядний пристрій, що призведе до того, що і батарея, і зарядний пристрій штовхатимуть струм в одному напрямку. Відбудеться несправність подачі, і клема PACK+ може опуститися нижче VSS та нижче від'ємного полюса батареї. Оскільки DSG не може опуститися нижче VSS мікросхеми, без Q6 затвор Q5 буде утримуватися поблизу VSS, тоді як джерело (PACK+) опускається зарядним пристроєм. Струм продовжує текти від батареї, оскільки Q5 працює як повторювач джерела — дивіться Рис. 2-1.

Зі схемою зворотного заряду Q6 при опусканні PACK+ нижче VSS, джерело Q6 опускається нижче його затвора, який утримується на рівні вище завдяки D7 та R27. Коли Q6 вмикається, він підтягує затвор Q5 до свого джерела, утримуючи FET розряду вимкненим. Оскільки DSG пристрою U1 не може опуститися нижче VSS, напруга падає на R24, який повинен бути вибраний для розсіювання необхідної потужності при заданій напрузі. D4 блокує струм через менший R25, який вибирається для швидкості вимикання Q5. DSG не призначений для подачі потужності, D3 пропускатиме струм замість виводу мікросхеми. Аналогічно виводи LD та PACK мікросхеми U1 не призначені для подачі потужності, D6 та D8 забезпечують шлях струму при примусовому опусканні PACK+ нижче VSS. Якщо PACK+ достатньо нижче VSS, D9 проводить, підтримуючи безпечну напругу VGS на затворі Q6 з додатковою напругою на R27. R28 утримує Q6 вимкненим, коли PACK+ перебуває в нормальному діапазоні. На Рис. 2-2 показаний приклад роботи схеми захисту від зворотного заряду.

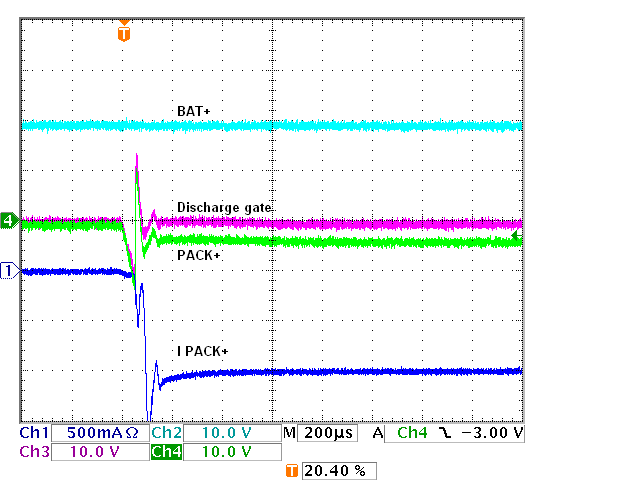
[picture p2: Documents/images/sluaan9a-000.png]
Рис. 2-1. Negative PACK+ без схеми захисту від зворотної зарядки


*Рис. 2-1. Negative PACK+ без схеми захисту від зворотної зарядки*

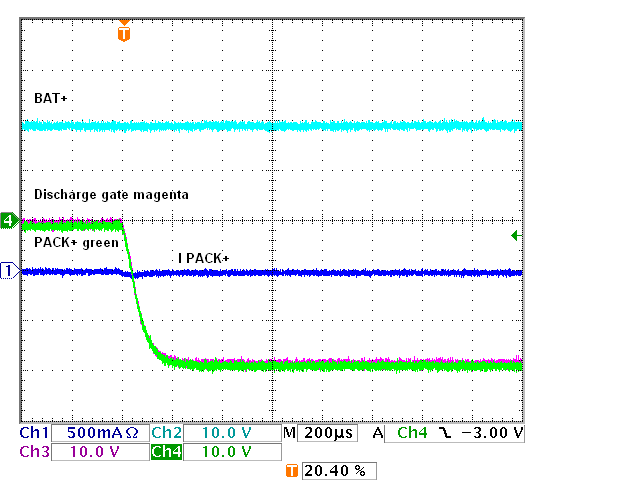
[picture p3: Documents/images/sluaan9a-002.png]
Рис. 2-2. Negative PACK+ зі схемою захисту від зворотної зарядки


*Рис. 2-2. Negative PACK+ зі схемою захисту від зворотної зарядки*

---

## 3 Вибір компонентів захисту від зворотної зарядки

Значення компонентів, що використовуються в тесті, показані на схемі Рис. 1-1. Розуміння роботи схеми легше, коли схема перемальована для чіткого відображення шляхів струму, як на Рис. 3-1.

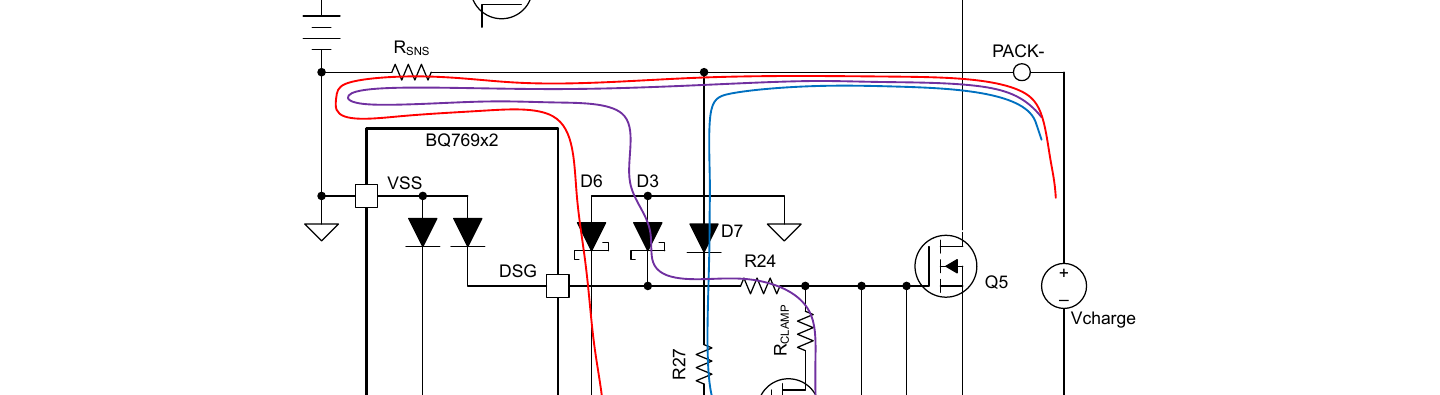
[picture p4: Documents/images/sluaan9a-fig3-1.png]
Рис. 3-1. Шляхи струму при зворотному заряді

![[Pasted image 20260403140707.png]]

*Рис. 3-1. Шляхи струму при зворотному заряді*

При підключеному зворотному зарядному пристрої клема PACK+ матиме значну від'ємну напругу. Основний шлях струму батареї не повинен проводити, а FET розряду Q5 повинен витримувати суму напруги батареї та напруги зворотного зарядного пристрою. У більшості випадків це буде щонайменше подвійна максимальна напруга батареї. Будь-який компонент, встановлений паралельно FET розряду, повинен мати аналогічний номінал.

Резистор виводу LD R29 повинен мати значення, рекомендоване в паспорті даних. При використанні резисторів із низьким номіналом потужності слід вибрати послідовну або паралельну комбінацію резисторів для досягнення потрібного опору та відповідного розсіювання потужності, коли PACK+ перебуває на найнижчому рівні. D6 запобігає протіканню струму та порушенню обмеження ABS MAX для виводу LD мікросхеми BQ769x2.

Транзистор Q6 затискає затвор FET розряду Q5 до його джерела, щоб утримувати FET розряду вимкненим під час застосування зворотного зарядного пристрою. D3 пропускає струм, щоб уникнути порушення обмеження ABS MAX виводу DSG. R24 повинен мати достатньо велике значення і достатній номінал потужності для підтримки напруги зворотного зарядного пристрою. R_CLAMP не показаний на Рис. 1-1, але включений до Рис. 3-1, оскільки він іноді використовується для уповільнення вимикання FET Q5 при опусканні PACK+ нижче PACK- через індуктивність навантаження при вимиканні. При використанні R_CLAMP він утворює дільник напруги разом з R24, і його значення повинно бути достатньо малим, щоб утримувати Q5 вимкненим під час застосування зворотного зарядного пристрою.

Транзистор Q6 вмикається напругою дільника, утвореного R27 та R28. Зазвичай R27 малий, а R28 великий, щоб напруга на затворі наростала швидко при опусканні PACK+ нижче нуля, а напруга затвора Q6 обмежувалась D9. R27 повинен бути достатньо великим для розсіювання потужності під час застосування зворотного зарядного пристрою, але блокує стік пакету через R27 при нормальній позитивній напрузі на PACK+. Ємність D7 також забезпечує ємнісний дільник разом із D9 і Ciss Q6, що може забезпечити достатню напругу на затворі Q6 для провідності при динамічних змінах PACK+. Якщо це є проблемою в конструкції, слід використовувати діод з малою ємністю для D7 або додати ємність до затвора Q6.

---

## 4 Зарядовий насос та ввімкнення FET

BQ76952 використовує зарядовий насос для забезпечення напруги, що перевищує напругу батарея+, для ввімкнення N-канальних MOSFET з боку високої напруги, що використовуються в системі. Летючий конденсатор зарядового насоса є внутрішнім, заряд зберігається у зовнішньому конденсаторі CP1 пристрою. CP1 є джерелом живлення для драйверів CHG та DSG. На Рис. 4-1 — 4-4 BQ76952 переведений у режим SHUTDOWN та пробуджується сигналом TS2. Коли зарядовий насос досягає напруги, він вимикається до тих пір, поки його напруга не впаде, і потім запускається знову. Часто можна побачити пульсацію на напрузі CP1 — повільне падіння з наступним швидким підйомом. На Рис. 4-1 зверніть увагу на повільне циклування перед ввімкненням FET та більш швидку пульсацію після ввімкнення FET з доданим навантаженням резисторів R_GS та навантаженням додаткових щупів осцилографа. На Рис. 4-2 показано більш детально нарощування зарядового насоса при низькій напрузі. Час наростання є більшим при нормальній напрузі, показаній на Рис. 4-3. Використання більшого конденсатора CP1 також збільшує час наростання, як на Рис. 4-4. Зверніть увагу, що зарядовий насос все ще перебуває в перехідному процесі, коли FET вмикаються. Використання конденсатора CP1 більше 2,2 мкФ не рекомендується з пристроями сімейства BQ769x2.

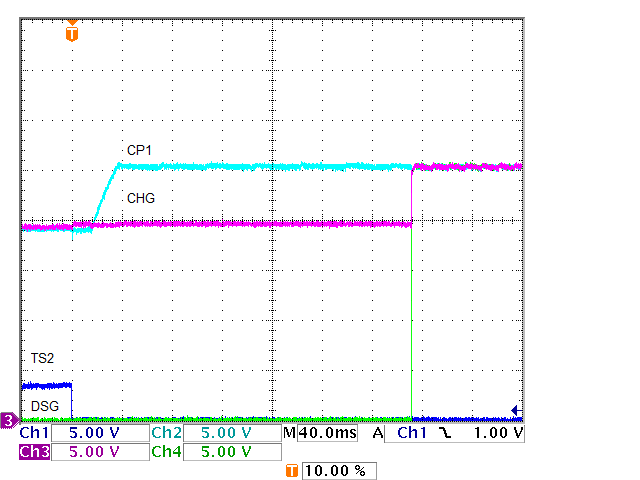
[picture p5: Documents/images/sluaan9a-004.png]
Рис. 4-1. Запуск зарядового насоса і ввімкнення FET, низька напруга, 470 нФ


*Рис. 4-1. Запуск зарядового насоса і ввімкнення FET, низька напруга, 470 нФ*

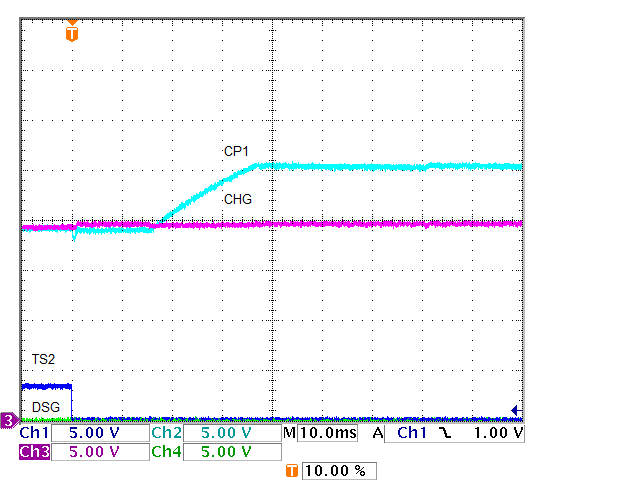
[picture p6: Documents/images/sluaan9a-006.png]
Рис. 4-2. Запуск зарядового насоса, низька напруга, 470 нФ


*Рис. 4-2. Запуск зарядового насоса, низька напруга, 470 нФ*

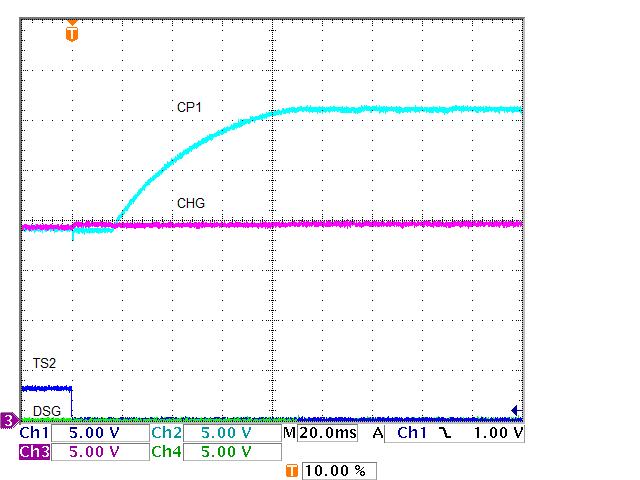
[picture p7: Documents/images/sluaan9a-008.png]
Рис. 4-3. Запуск зарядового насоса, нормальна напруга, 470 нФ


*Рис. 4-3. Запуск зарядового насоса, нормальна напруга, 470 нФ*

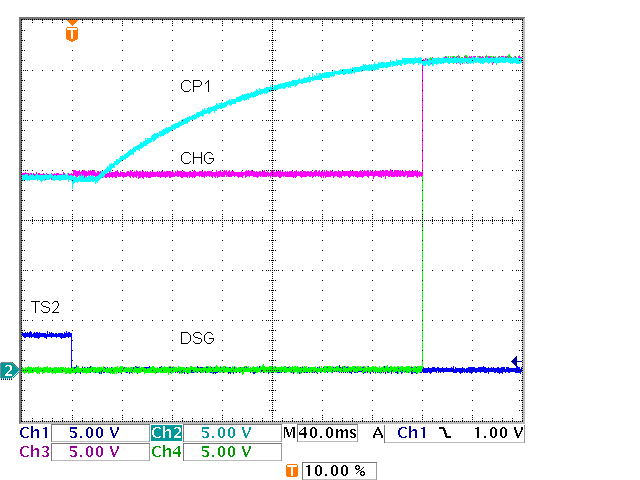
[picture p8: Documents/images/sluaan9a-010.png]
Рис. 4-4. Запуск зарядового насоса і ввімкнення FET, CP1 2 мкФ


*Рис. 4-4. Запуск зарядового насоса і ввімкнення FET, CP1 2 мкФ*

Округла форма сигналу CP1 при запуску вказує на те, що зарядовий насос може видавати більший струм при нижчій напрузі. CP1 є джерелом живлення для драйверів FET з боку високої напруги. Коли CHG або DSG вмикаються, струм для CHG та DSG для ввімкнення FET надходить з конденсатора CP1. Як наближення з ідеальним перемиканням, заряд не втрачається, і заряд на конденсаторі CP1 до ввімкнення розподіляється між CP1 та затворною ємністю FET після ввімкнення.

$$Q = V_1 \times C_{CP1} = V_2 \times (C_{CP1} + N \times C_{iss}) \tag{1}$$

Тоді напруга після ввімкнення буде пропорцією початкової напруги:

$$V_2 = V_1 \times C_{CP1} / (C_{CP1} + N \times C_{iss}) \tag{2}$$

де:
- V1 — напруга зарядового насоса перед комутацією FET
- V2 — напруга зарядового насоса та затвора FET після комутації FET
- $C_{CP1}$ — конденсатор зарядового насоса
- N — кількість FET, що перемикаються
- Ciss — затворна ємність використовуваного FET

Зарядовому насосу знадобиться час для поповнення заряду, переданого до затворів, та повернення напруги до регульованого діапазону CP1. На Рис. 4-5 показано просідання напруги зарядового насоса при ввімкненні 24 FET CSD19536KCS при використанні 470 нФ для $C_{CP1}$. На Рис. 4-6 показано менше просідання при ввімкненні тих самих 24 FET при використанні 2 мкФ для $C_{CP1}$.

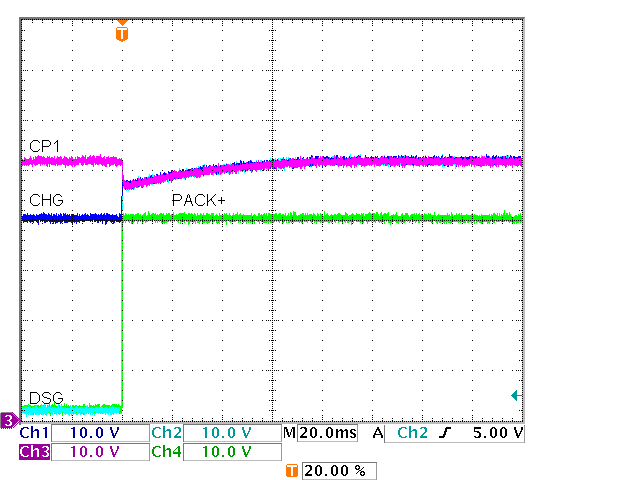
[picture p9: Documents/images/sluaan9a-012.png]
Рис. 4-5. Просідання CP1, 24 FET, C_CP1 470 нФ


*Рис. 4-5. Просідання CP1, 24 FET, $C_{CP1}$ 470 нФ*

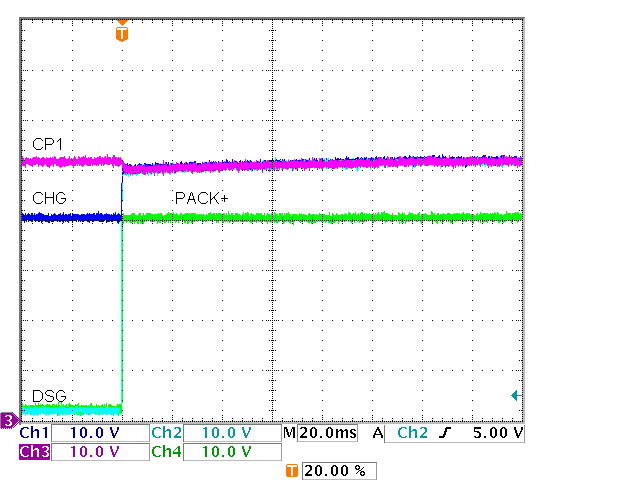
[picture p10: Documents/images/sluaan9a-014.png]
Рис. 4-6. Просідання CP1, 24 FET, C_CP1 2 мкФ


*Рис. 4-6. Просідання CP1, 24 FET, $C_{CP1}$ 2 мкФ*

---

## 5 Тестові схеми з паралельними FET

Коли FET працюють паралельно, вони можуть осцилювати при перемиканні. У індивідуальному шляху затвора часто використовується невеликий опір або феритова намистина для запобігання осциляції. На Рис. 5-1 показана тестова схема з кількома FET. Резистори 51 Ом використовуються в тестових схемах цього прикладного звіту для ізоляції окремих затворів від загальних ліній Cgate та Dgate. Cgate та Dgate зазвичай використовуються на рисунках у цьому документі, а не індивідуальна напруга затвора, якщо не зазначено інше. При використанні одного FET резистор 51 Ом залишається. FET заповнюються за необхідністю, решта схеми BQ769x2 залишається незмінною. FET CSD19536KCS, що використовуються в цій прикладній нотатці, мають типове значення Ciss 9,25 нФ. R41 та R44 регулюються залежно від кількості FET. Схема захисту від зворотного заряду збережена у тестових схемах з паралельними FET, Q29 є фіксуючим FET.

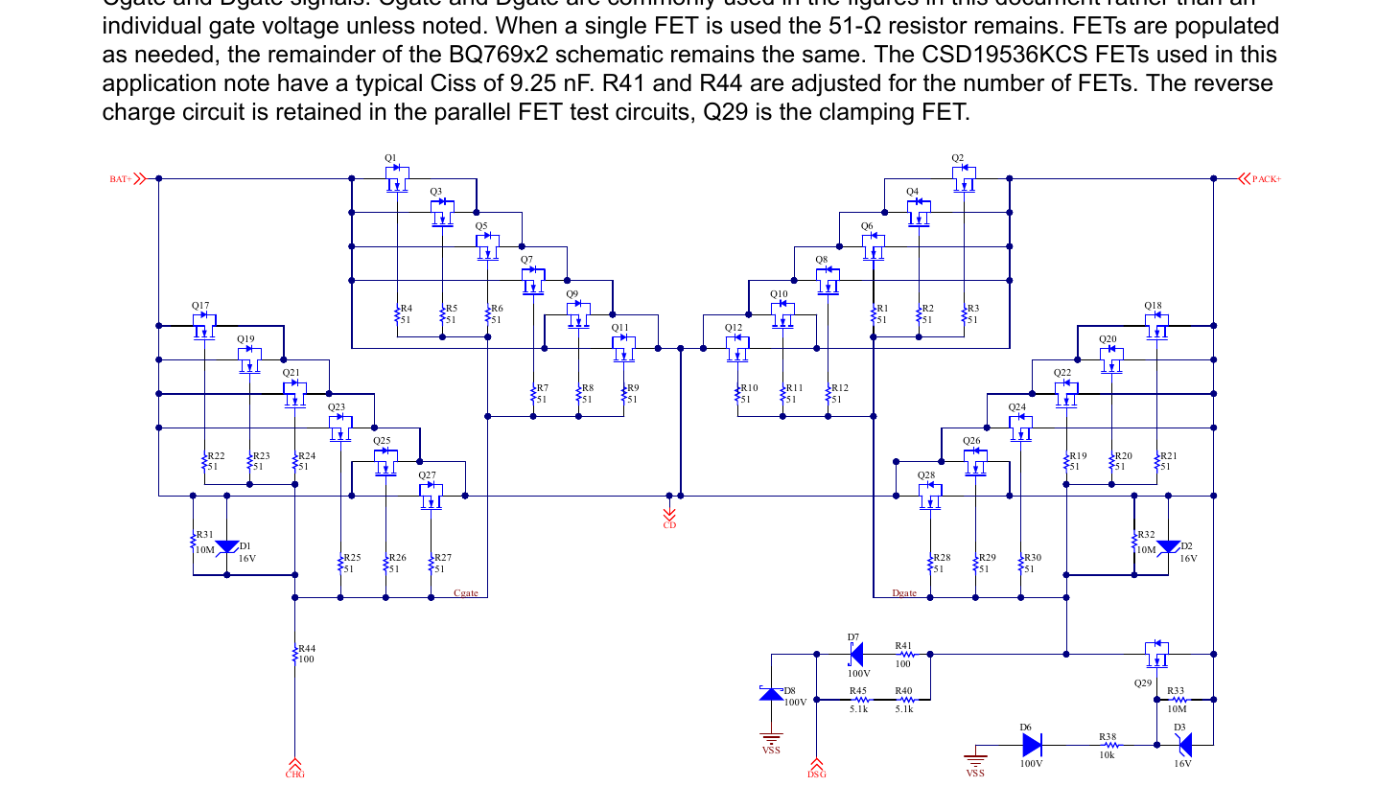
[picture p11: Documents/images/sluaan9a-fig5-1.png]
Рис. 5-1. Тестова схема з кількома FET


![[Pasted image 20260402193022.png]]

*Рис. 5-1. Тестова схема з кількома FET*

BQ769x2 має внутрішні опори драйверів, тому для більших навантажень можна використовувати локальну схему вимкнення. На Рис. 5-2 показана схема, в якій PNP-транзистори використовуються для забезпечення локального контуру струму для вимкнення FET. Це дозволяє вимикати з меншим локальним контуром через транзистор і зовнішній опір. При вимиканні FET заряду CHG відбирає базовий струм від Q30 через R44, тоді як колекторний струм розряджає затвори FET заряду через R35. Аналогічно DSG відбирає базовий струм для Q31 через комбінацію R40, R45, R41 та D7. Колекторний струм розряджає затвори FET через R37. Ввімкнення все ще відбувається від конденсатора зарядового насоса через D4 для CHG та D5 для DSG. Якщо падіння напруги на D4 та D5 є проблемою, можна використовувати діод Шоттки або додати великий паралельний резистор для підняття затворів до повної напруги після початкового стрибка струму.

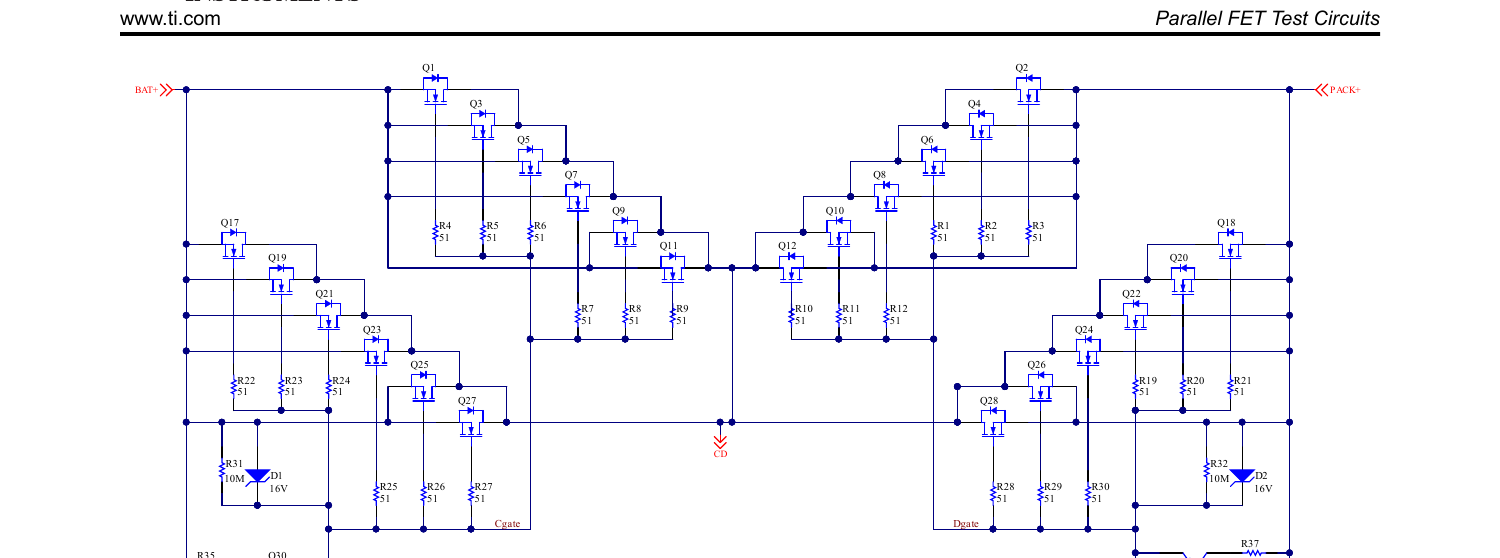
[picture p12: Documents/images/sluaan9a-fig5-2.png]
Рис. 5-2. Тестова схема з кількома FET з локальними контурами струму

![[Pasted image 20260403140523.png]]

*Рис. 5-2. Тестова схема з кількома FET з локальними контурами струму*

---

## 6 Драйвер CHG

Драйвер заряду працює між рівнем виводу BAT та напругою CP1. На Рис. 6-1 — 6-18 показані приклади комутації драйвера заряду при різній кількості FET з різними підключеннями схеми. У багатьох осцилограмах струм та деякі напруги показують пульсацію, де підключене обладнання встановлювалось у режим регулювання з новим навантаженням. Приклади осцилограм заряду зроблені при 20 В та струмі заряду 1 А.

На Рис. 6-1 — 6-4 показано ввімкнення та вимкнення одного та двох FET при R44 = 5,1 кОм. Додаткова ємність другого затвора уповільнює ввімкнення та вимкнення.

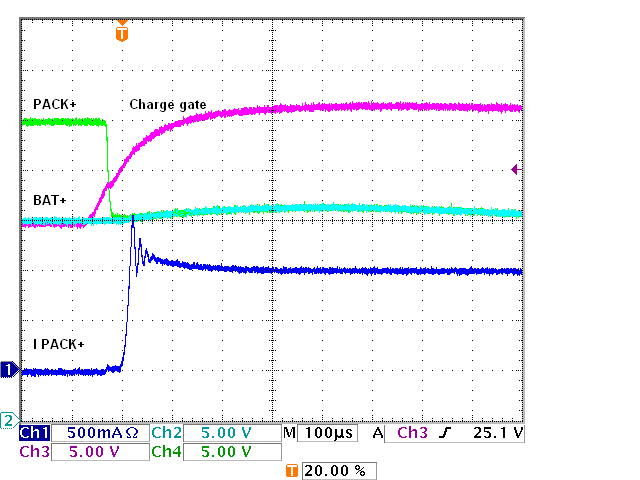
[picture p13: Documents/images/sluaan9a-016.png]
Рис. 6-1. CHG Увімк., 1 FET, 5,1 кОм, 470 нФ


*Рис. 6-1. CHG Увімк., 1 FET, 5,1 кОм, 470 нФ*

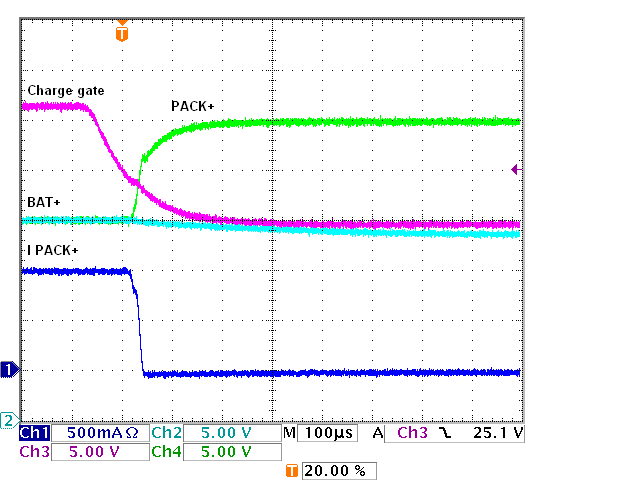
[picture p14: Documents/images/sluaan9a-018.png]
Рис. 6-2. CHG Вимк., 1 FET, 5,1 кОм


*Рис. 6-2. CHG Вимк., 1 FET, 5,1 кОм*

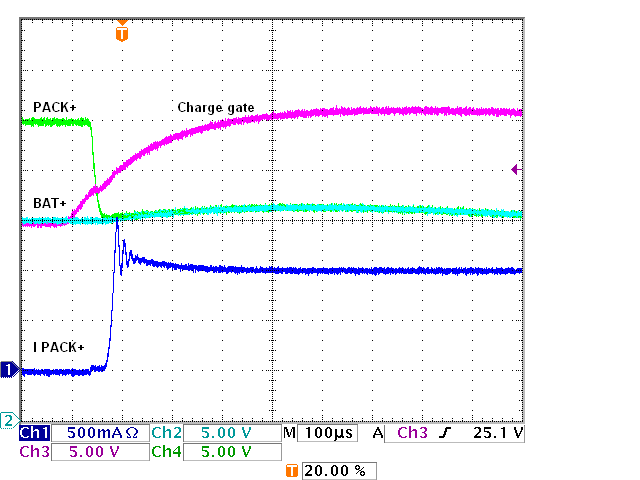
[picture p15: Documents/images/sluaan9a-020.png]
Рис. 6-3. CHG Увімк., 2 FET, 5,1 кОм, 470 нФ


*Рис. 6-3. CHG Увімк., 2 FET, 5,1 кОм, 470 нФ*

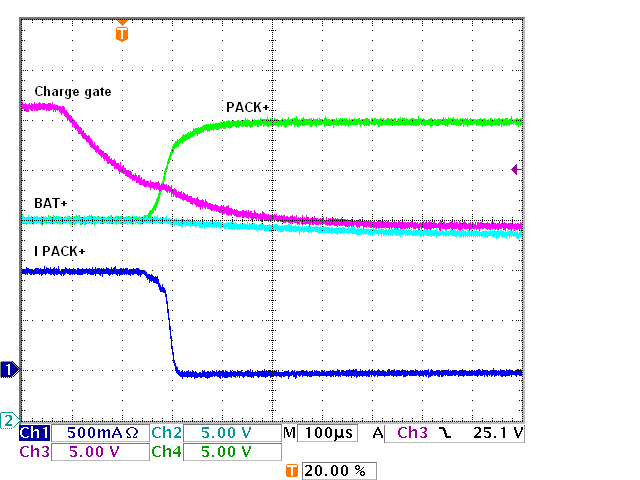
[picture p16: Documents/images/sluaan9a-022.png]
Рис. 6-4. CHG Вимк., 2 FET, 5,1 кОм


*Рис. 6-4. CHG Вимк., 2 FET, 5,1 кОм*

На Рис. 6-5 — 6-8 показано ввімкнення та вимкнення при заміні R44 на 1 кОм, потім 100 Ом. Можна спостерігати різницю між виводом CHG та загальною сіткою затвора заряду (Cgate). Менший резистор керує затвором швидше, а більше навантаження на затвор уповільнює перехід виводу.

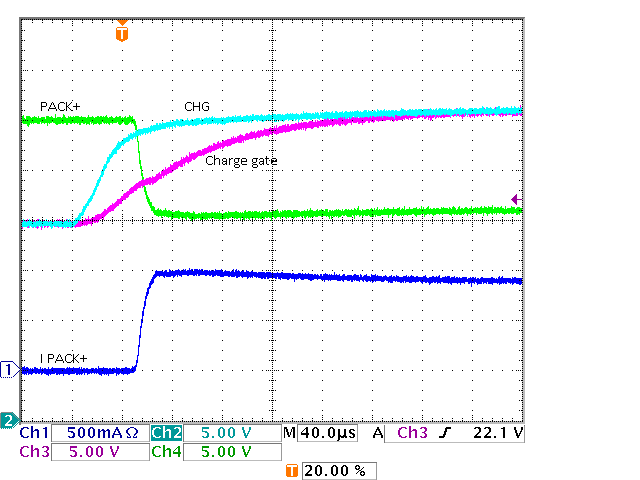
[picture p17: Documents/images/sluaan9a-024.png]
Рис. 6-5. CHG Увімк., 1 FET, 1 кОм, 470 нФ


*Рис. 6-5. CHG Увімк., 1 FET, 1 кОм, 470 нФ*

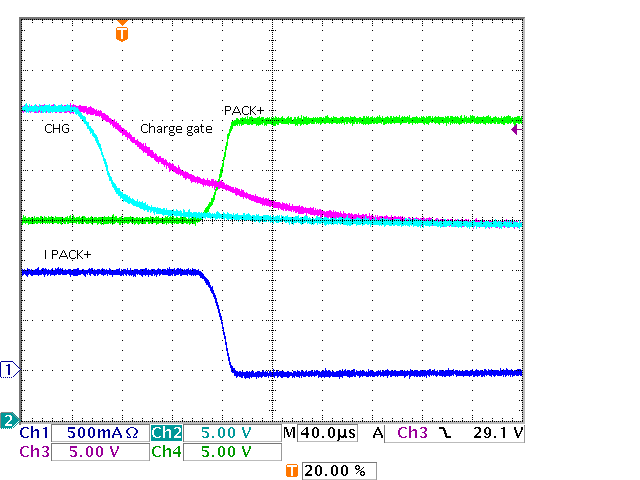
[picture p18: Documents/images/sluaan9a-026.png]
Рис. 6-6. CHG Вимк., 1 FET, 1 кОм


*Рис. 6-6. CHG Вимк., 1 FET, 1 кОм*

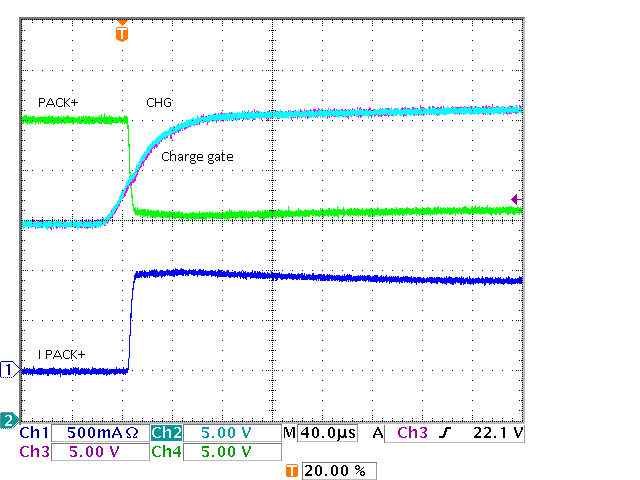
[picture p19: Documents/images/sluaan9a-028.png]
Рис. 6-7. CHG Увімк., 1 FET, 100 Ом, 470 нФ


*Рис. 6-7. CHG Увімк., 1 FET, 100 Ом, 470 нФ*

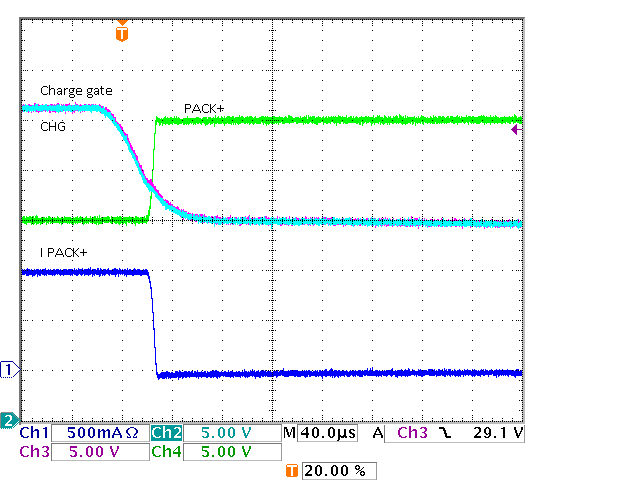
[picture p20: Documents/images/sluaan9a-030.png]
Рис. 6-8. CHG Вимк., 1 FET, 100 Ом


*Рис. 6-8. CHG Вимк., 1 FET, 100 Ом*

При більшій кількості FET перемикання уповільнюється, оскільки опір діє на затворну ємність. На Рис. 6-9 показано вимкнення 4 FET при R44 = 100 Ом. Для більш швидкого перемикання локальний контур струму, створений PNP-транзистором, керованим виводом CHG мікросхеми BQ769x2, показаний на Рис. 5-2, дозволяє затвору розряджатися через менший опір для більш швидкого переходу, як показано на Рис. 6-10. R44 залишається рівним 100 Ом для цього прикладу.

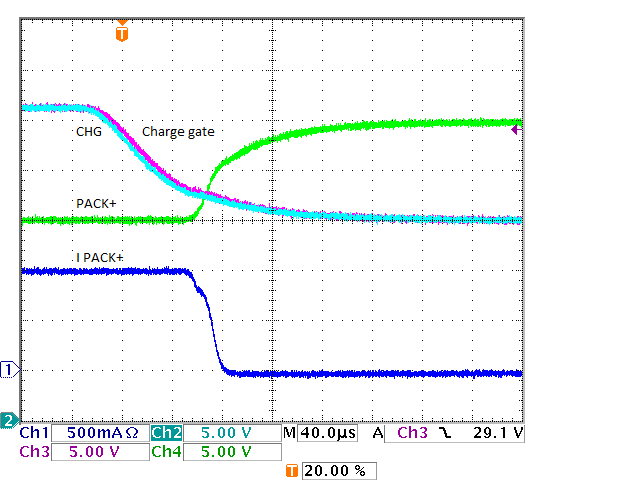
[picture p21: Documents/images/sluaan9a-032.png]
Рис. 6-9. CHG Вимк., 4 FET, 100 Ом


*Рис. 6-9. CHG Вимк., 4 FET, 100 Ом*

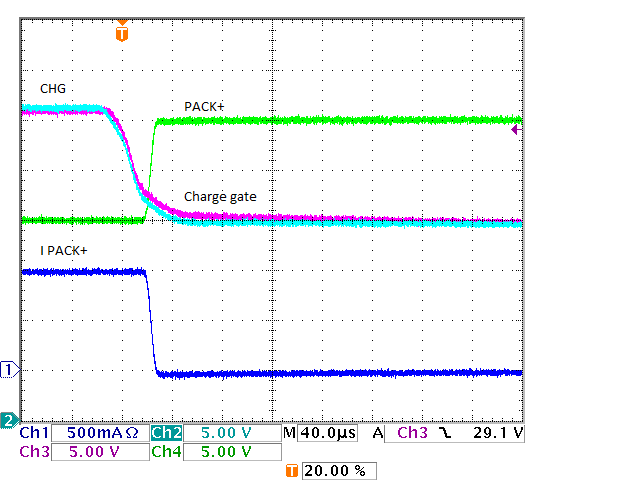
[picture p22: Documents/images/sluaan9a-034.png]
Рис. 6-10. CHG Вимк., 4 FET, 100 Ом, PNP


*Рис. 6-10. CHG Вимк., 4 FET, 100 Ом, PNP*

Перемикання 8 FET з R44 = 100 Ом і без PNP показано на Рис. 6-11. Повільний перехід вказував би на те, що більшість опору є внутрішнім для драйвера CHG. На Рис. 6-12 показано, що навіть з R44 = 5,1 кОм час вимкнення є швидшим, оскільки CHG відбирає лише базовий струм для PNP. 5,1-кОм R44 діє повільно при ввімкненні, як показано на Рис. 6-13; використання R44 = 100 Ом на Рис. 6-14 збільшує швидкість ввімкнення, хоча 100 Ом не були потрібні для вимкнення.

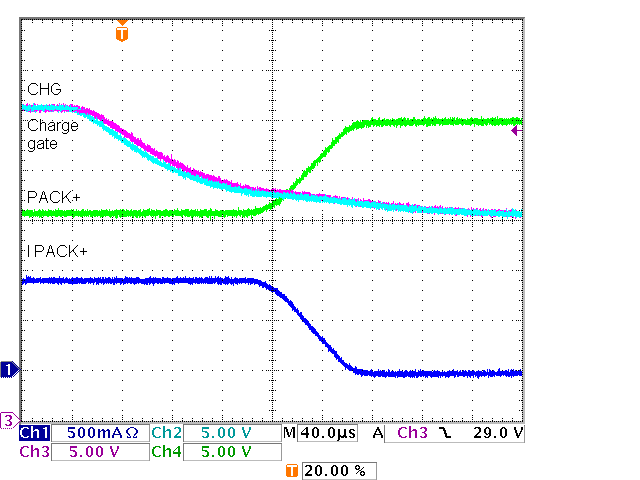
[picture p23: Documents/images/sluaan9a-036.png]
Рис. 6-11. CHG Вимк., 8 FET, 100 Ом


*Рис. 6-11. CHG Вимк., 8 FET, 100 Ом*

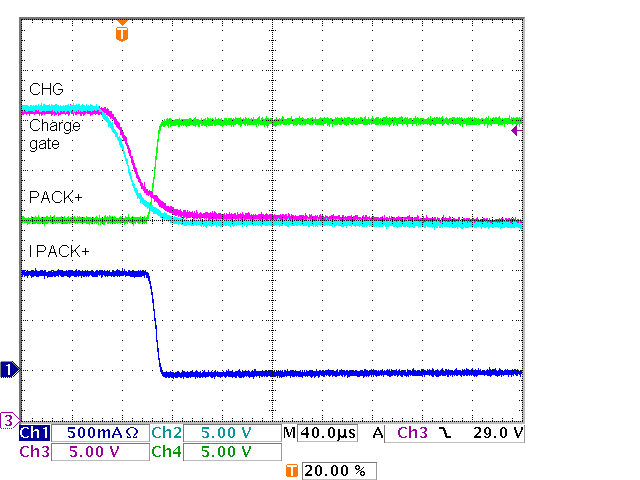
[picture p24: Documents/images/sluaan9a-038.png]
Рис. 6-12. CHG Вимк., 8 FET, 5,1 кОм, PNP


*Рис. 6-12. CHG Вимк., 8 FET, 5,1 кОм, PNP*

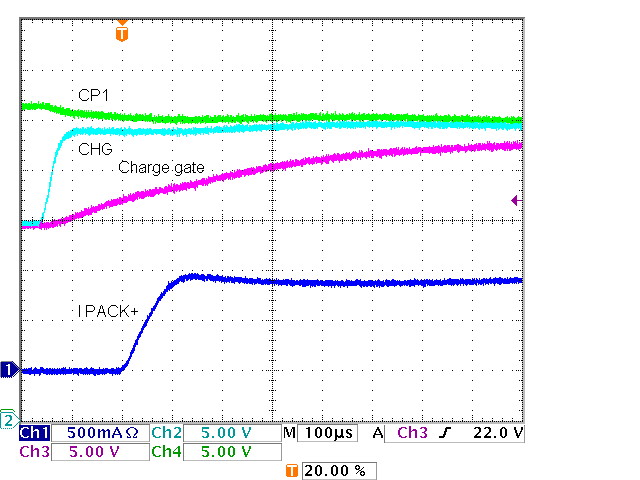
[picture p25: Documents/images/sluaan9a-040.png]
Рис. 6-13. CHG Увімк., 8 FET, 5,1 кОм, PNP, 470 нФ


*Рис. 6-13. CHG Увімк., 8 FET, 5,1 кОм, PNP, 470 нФ*

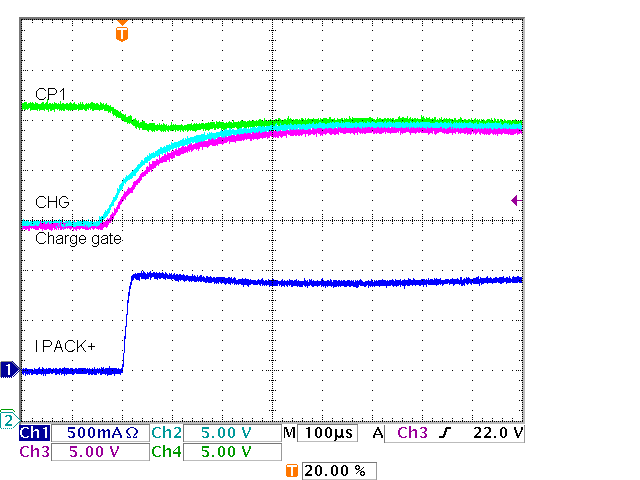
[picture p26: Documents/images/sluaan9a-042.png]
Рис. 6-14. CHG Увімк., 8 FET, 100 Ом, PNP, 470 нФ


*Рис. 6-14. CHG Увімк., 8 FET, 100 Ом, PNP, 470 нФ*

У більш широкому масштабі часу Рис. 6-15 та Рис. 6-16 показують вплив розміру конденсатора зарядового насоса на перемикання 8 FET.

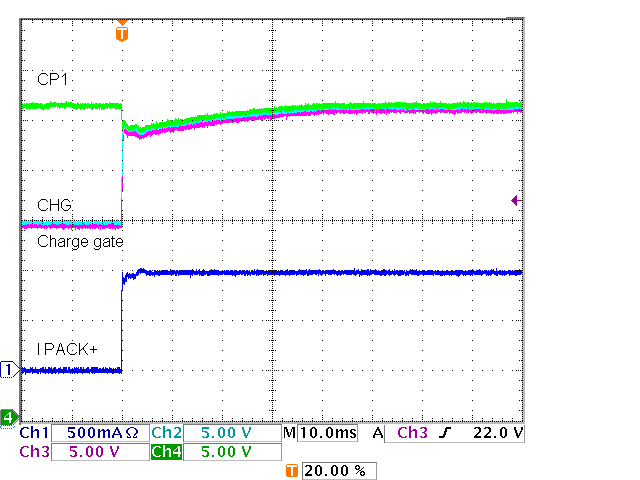
[picture p27: Documents/images/sluaan9a-044.png]
Рис. 6-15. CHG Увімк., 8 FET, 100 Ом, PNP, 470 нФ


*Рис. 6-15. CHG Увімк., 8 FET, 100 Ом, PNP, 470 нФ*

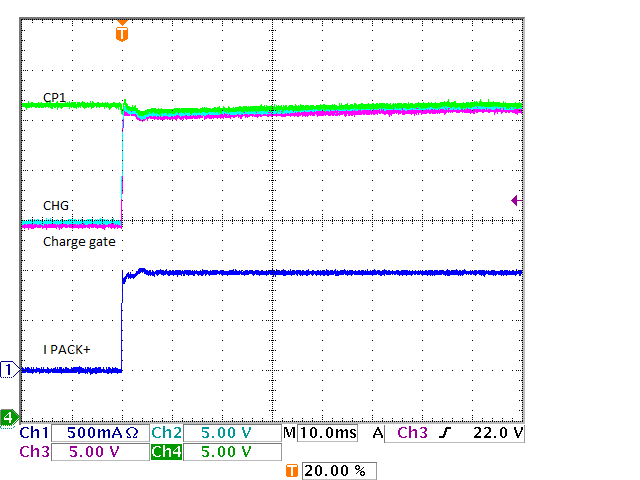
[picture p28: Documents/images/sluaan9a-046.png]
Рис. 6-16. CHG Увімк., 8 FET, 100 Ом, PNP, 2 мкФ


*Рис. 6-16. CHG Увімк., 8 FET, 100 Ом, PNP, 2 мкФ*

При ємності CP1 2 мкФ на Рис. 6-17 та Рис. 6-18 показано ввімкнення та вимкнення 12 FET з R44 = 100 Ом та схемою PNP. Регулювання швидкості вимкнення за допомогою значення R35 у цьому звіті не показане.

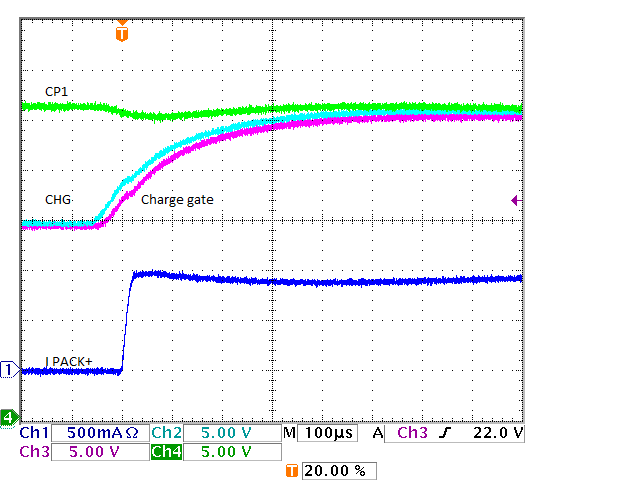
[picture p29: Documents/images/sluaan9a-048.png]
Рис. 6-17. CHG Увімк., 12 FET, 100 Ом, PNP, 2 мкФ


*Рис. 6-17. CHG Увімк., 12 FET, 100 Ом, PNP, 2 мкФ*

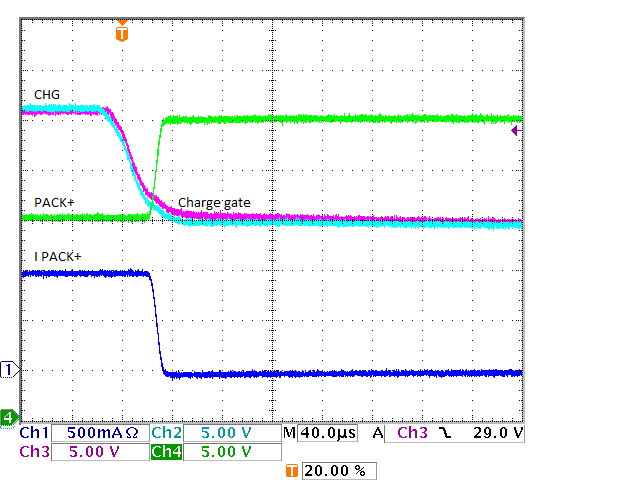
[picture p30: Documents/images/sluaan9a-050.png]
Рис. 6-18. CHG Вимк., 12 FET, 100 Ом, PNP


*Рис. 6-18. CHG Вимк., 12 FET, 100 Ом, PNP*

---

## 7 Шляхи струму драйвера CHG

Сила драйвера CHG є поширеним питанням, але не має простої відповіді. Драйвер був розроблений для забезпечення керованого ввімкнення та вимкнення FET із навантажувальною ємністю. Він не оцінюється в амперах, як деякі драйвери затворів загального призначення, і не характеризується опором, але характеризується часами наростання та спадання, показаними в паспорті даних. При ввімкненні CHG струм тече від конденсатора CP1 через вивід CHG до затворів FET, як показано на Рис. 7-1. Вимірювання при малому струмі може показати внутрішній опір від 1 до 2 кОм, але перемикач не є лінійним і обмежуватиме струм. Зарядовий насос забезпечує обмежений струм, тому струм для заряду затворів FET надходить від конденсатора CP1 — C15, і розподіляє заряд від конденсатора CP1 до ємностей конденсатора та затворів. Більший конденсатор CP1 допустить менше просідання при ввімкненні, як було показано раніше на Рис. 6-15 та Рис. 6-16. Струм від конденсатора CP1 C15 підтримується C12 та поповнюється струмом через D1 та R11. Резистор виводу CHG $R_{GATE}$ (R17) не рекомендується нижче 100 Ом для забезпечення деякої ізоляції виводу від шляху струму.

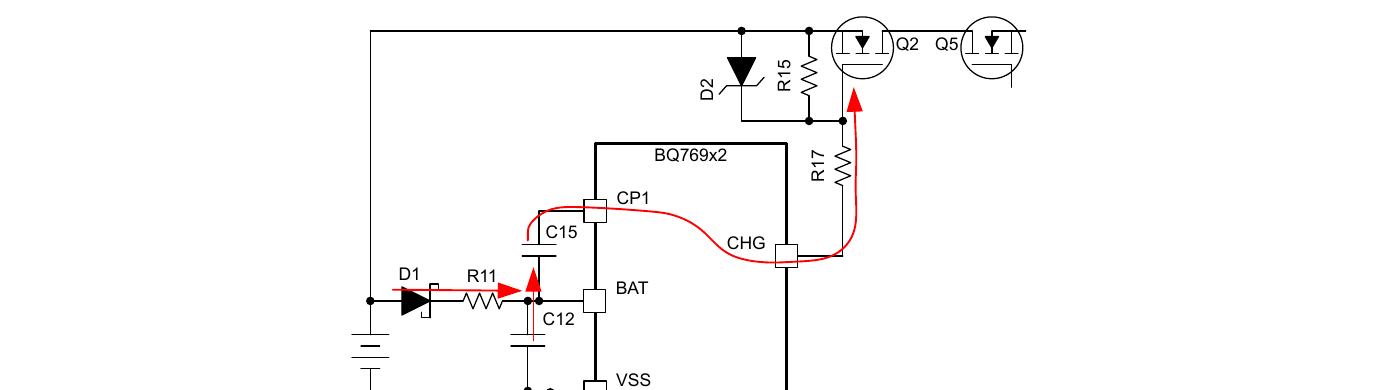
[picture p31: Documents/images/sluaan9a-fig7-1.png]
Рис. 7-1. Шлях струму ввімкнення драйвера CHG


*Рис. 7-1. Шлях струму ввімкнення драйвера CHG*

Коли BQ769x2 перебуває в режимі SHUTDOWN, вивід CHG може опускатись до VSS. Однак у нормальній схемі стабілітрон затвор-джерело FET заряду D2 та резистор R15 утримуватимуть напругу виводу CHG на рівні напруги батареї.

Типовий рекомендований резистор затвор-джерело (R15) становить 10 МОм, забезпечуючи навантаження приблизно 1,1 мкА при роботі зарядового насоса на рівні $V_{(FETON\_HI)}$. Хоча будь-яке навантаження спричинить деяке просідання напруги зарядового насоса, зарядовий насос зазвичай може підтримувати 10 В при навантаженні на драйвери приблизно до 40 мкА. Зарядовий насос спільний із драйвером DSG, тому його навантаження також слід враховувати. При завантаженні драйвера CHG його напруга впаде, що також призведе до падіння напруги на виводі DSG, якщо DSG також увімкнений. Приклад показано на Рис. 7-2. Зарядовий насос може подавати приблизно 200 мкА у заземлений резистор затвор-джерело. Там є коефіцієнт посилення по потоку приблизно 6, тому струм виводу BAT збільшиться приблизно на 1200 мкА для забезпечення 200 мкА до CHG. Коли драйвер CHG відтягується нижче, він впаде нижче напруги виводу BAT, і струм обмежуватиметься. При реалізації схеми для перевизначення виводу CHG слід передбачити деякий запас вище можливостей зарядового насоса, щоб переконатись у вимиканні FET заряду. Також враховуйте відтягування DSG: знижена напруга залишить FET розряду у режимі повторювача джерела. Може бути корисним сигналізувати вимкнення виходу DSG FET через вхід DFETOFF мікросхеми BQ769x2, де це доступно.

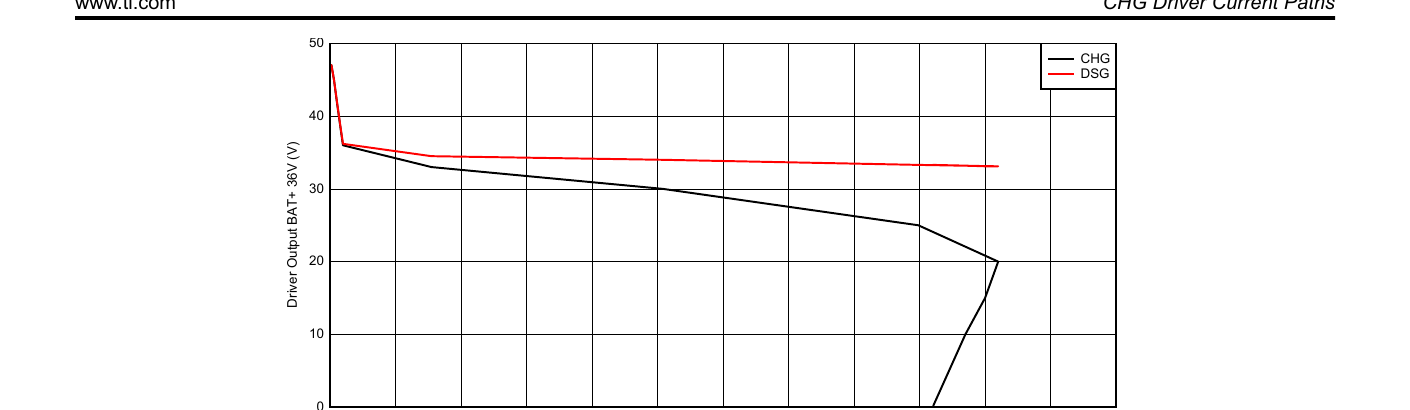
[picture p32: Documents/images/sluaan9a-fig7-2.png]
Рис. 7-2. CHG під навантаженням при батареї 36 В


*Рис. 7-2. CHG під навантаженням при батареї 36 В*

Коли драйвер CHG вимикається, CHG підтягується до виводу BAT, і Ciss FET заряду розряджається до ємності виводу BAT C12, як показано на Рис. 7-3. Відтягування виглядатиме приблизно як 1 кОм, але буде варіюватися залежно від напруги. Це може тимчасово підвищити напругу на виводі BAT до тих пір, поки струм навантаження BQ769x2 не знизить напругу BAT до нормального рівня. Приклад підйому виводу BAT при вимиканні з 4 FET показано на Рис. 7-4. C12 не слід робити меншим за типовий 1 мкФ для запобігання підвищенню напруги BAT. Використання локальної схеми контуру струму зменшить струм, що надходить до C12, і результуючий підйом напруги, крім прискорення вимкнення FET заряду, як показано у порівнянні між Рис. 6-9 та Рис. 6-10.

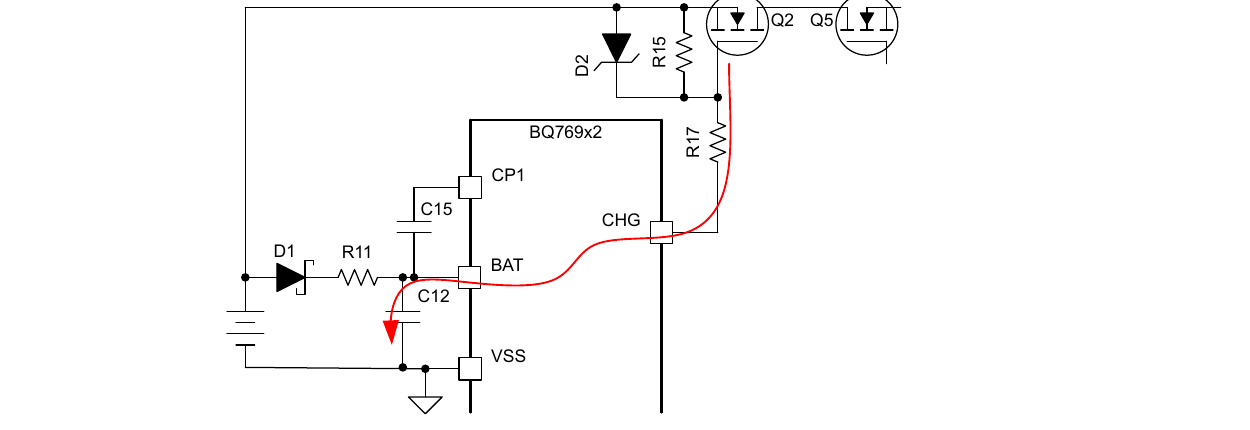
[picture p33: Documents/images/sluaan9a-fig7-3.png]
Рис. 7-3. Шлях струму вимикання драйвера CHG


*Рис. 7-3. Шлях струму вимикання драйвера CHG*

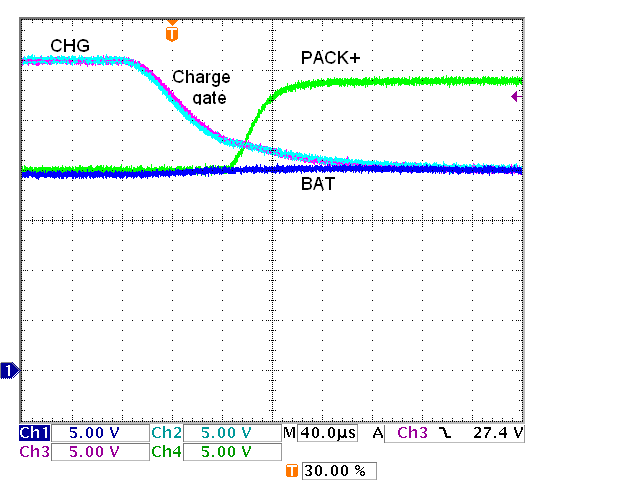
[picture p34: Documents/images/sluaan9a-052.png]
Рис. 7-4. CHG Вимк., 4 FET, 100 Ом, без струму


*Рис. 7-4. CHG Вимк., 4 FET, 100 Ом, без струму*

---

## 8 Драйвер DSG

Драйвер розряду працює між VSS та напругою CP1. Коли драйвер вмикається, DSG піднімається до напруги CP1, оскільки струм тече через R45 та R40 зі Рис. 5-1. R45 та R40 забезпечують опір ввімкнення 10 кОм. Приклад ввімкнення одного FET показано на Рис. 8-1. При ввімкненні FET піднімається PACK+, і через FET розряду протікає струм. Напруга затвора відставатиме від напруги DSG з фільтруючим ефектом опору ввімкнення та затворної ємності.

Коли драйвер DSG спрацьовує для вимкнення, пристрій спочатку почне розряджати вивід DSG до VSS. Однак, оскільки клема PACK+ може не швидко впасти до напруги поблизу VSS, затвор FET DSG не повинен опускатись значно нижче PACK+, інакше FET DSG може бути пошкоджений через надмірну від'ємну напругу затвор-джерело, або вивід DSG спробує розрядити PACK+ через резистор затвор-джерело або стабілітрон. Тому пристрій контролює напругу на виводі LD (який підключений до PACK+ через зовнішній послідовний резистор) і зупиняє розряд, коли напруга виводу DSG падає нижче напруги виводу LD. Коли розряд зупинився, напруга може знову піднятись вище напруги виводу LD, і пристрій знову розрядить вивід DSG до VSS, поки напруга затвора DSG знову не впаде нижче напруги виводу LD. Це повторюється серією імпульсів, які з часом розряджають затвор DSG до напруги виводу LD. Це тривання тривалістю приблизно 200 мкс, після чого драйвер залишається у стані з високим імпедансом нижче напруги виводу LD плюс приблизно 500 мВ. Зовнішній резистор між затвором та джерелом DSG потім розряджає залишкову напругу, щоб FET залишався вимкненим.

Приклад вимкнення показано на Рис. 8-2. Відтягування DSG відбирає струм із затвора FET через діод Шоттки D7 та R41. Додатковий струм протікатиме через R40 та R45. Струм, що надходить до виводу DSG, надходить до виводу VSS, а не до виводу LD. На Рис. 8-1 та Рис. 8-2 показана напруга затвора одного FET, а не загальна напруга сітки затворів, оскільки є лише 1 FET.

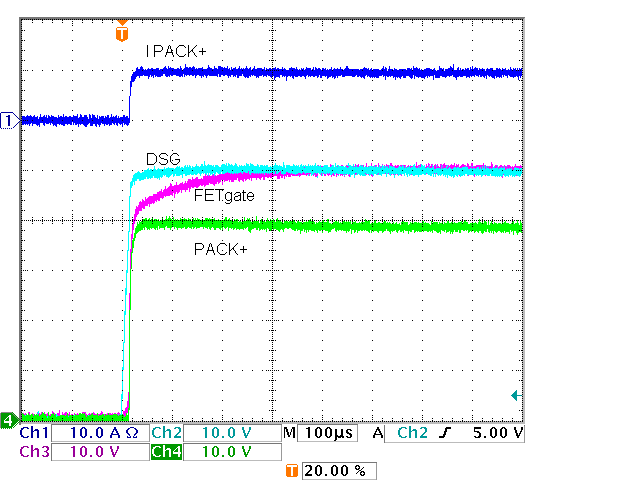
[picture p35: Documents/images/sluaan9a-054.png]
Рис. 8-1. DSG Увімк., 1 FET, 10 кОм, 470 нФ


*Рис. 8-1. DSG Увімк., 1 FET, 10 кОм, 470 нФ*

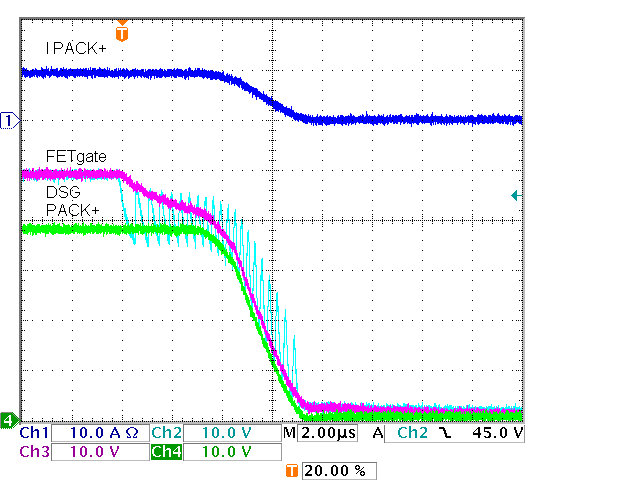
[picture p36: Documents/images/sluaan9a-056.png]
Рис. 8-2. DSG Вимк., 1 FET, R41 100 Ом


*Рис. 8-2. DSG Вимк., 1 FET, R41 100 Ом*

Перевіряючи напругу батареї на Рис. 8-3, імпульсування дозволяє уникнути швидкого вимкнення та результуючого великого індуктивного стрибка. Розробник повинен вибрати швидкість вимкнення, придатну для індуктивності батареї. При цьому тестовому струмі напруга батареї зросла на 4 В; для порівняння кількості FET буде використано більше значення R41.

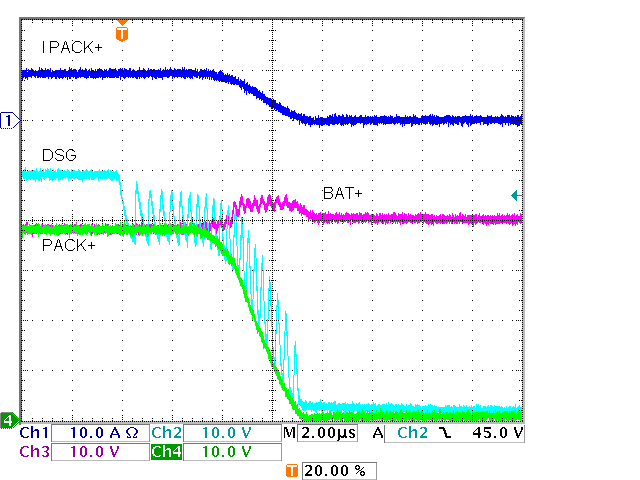
[picture p37: Documents/images/sluaan9a-058.png]
Рис. 8-3. Перехідний процес батареї, 1 FET, R41 100 Ом


*Рис. 8-3. Перехідний процес батареї, 1 FET, R41 100 Ом*

На Рис. 8-4 — 8-9 показані приклади ввімкнення та вимкнення зі схемою зворотного заряду, R41 = 1 кОм, та 1–4 FET. Ввімкнення для одного FET аналогічне випадку з R41 = 100 Ом, оскільки діод Шоттки блокує струм у R41 при ввімкненні. На Рис. 8-4 спостерігається загальна сітка затворів, а не затвор одного FET.

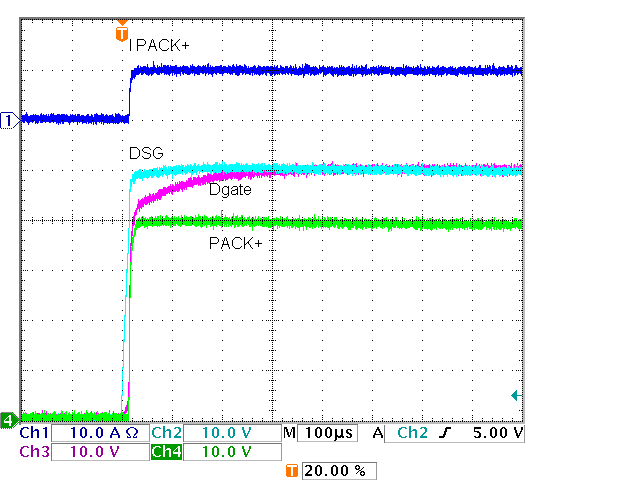
[picture p38: Documents/images/sluaan9a-060.png]
Рис. 8-4. DSG Увімк., 1 FET, 10 кОм, 470 нФ


*Рис. 8-4. DSG Увімк., 1 FET, 10 кОм, 470 нФ*

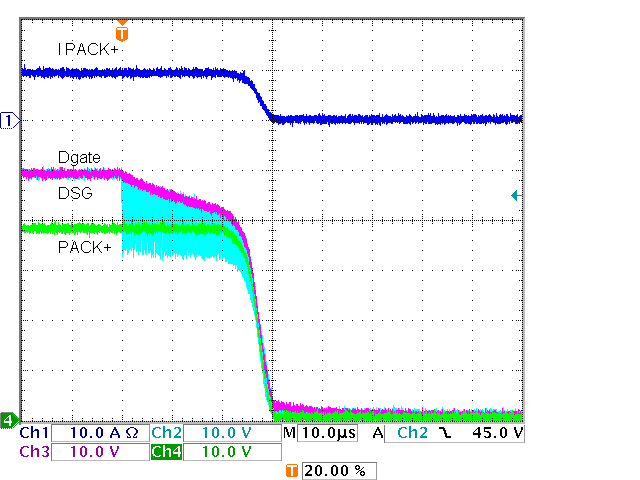
[picture p39: Documents/images/sluaan9a-062.png]
Рис. 8-5. DSG Вимк., 1 FET, R41 1 кОм


*Рис. 8-5. DSG Вимк., 1 FET, R41 1 кОм*

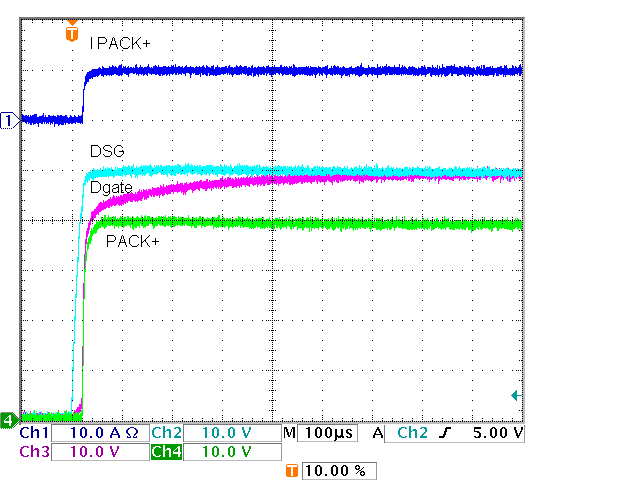
[picture p40: Documents/images/sluaan9a-064.png]
Рис. 8-6. DSG Увімк., 2 FET, 10 кОм, 470 нФ


*Рис. 8-6. DSG Увімк., 2 FET, 10 кОм, 470 нФ*

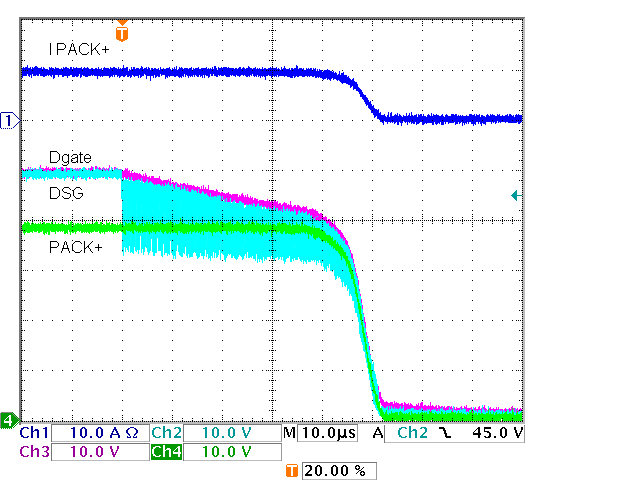
[picture p41: Documents/images/sluaan9a-066.png]
Рис. 8-7. DSG Вимк., 2 FET, R41 1 кОм


*Рис. 8-7. DSG Вимк., 2 FET, R41 1 кОм*

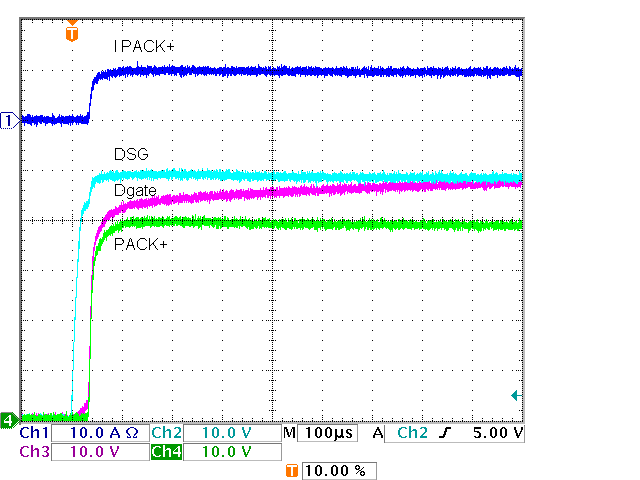
[picture p42: Documents/images/sluaan9a-068.png]
Рис. 8-8. DSG Увімк., 4 FET, 10 кОм, 470 нФ


*Рис. 8-8. DSG Увімк., 4 FET, 10 кОм, 470 нФ*

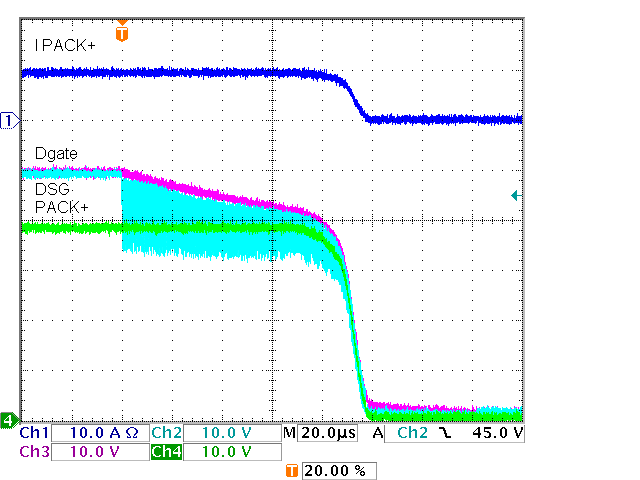
[picture p43: Documents/images/sluaan9a-070.png]
Рис. 8-9. DSG Вимк., 4 FET, R41 1 кОм


*Рис. 8-9. DSG Вимк., 4 FET, R41 1 кОм*

При 8 FET затворна ємність збільшила розрив між сіткою DSG та Dgate при ввімкненні та уповільнила наростання, як показано на Рис. 8-10. На Рис. 8-11 FET не вимикаються під час часу імпульсування виводу DSG, а пізніше — від слабкого відтягування DSG. Час вимкнення значно збільшується, і вимкнення є повільним. Цієї умови слід уникати в конструкції.

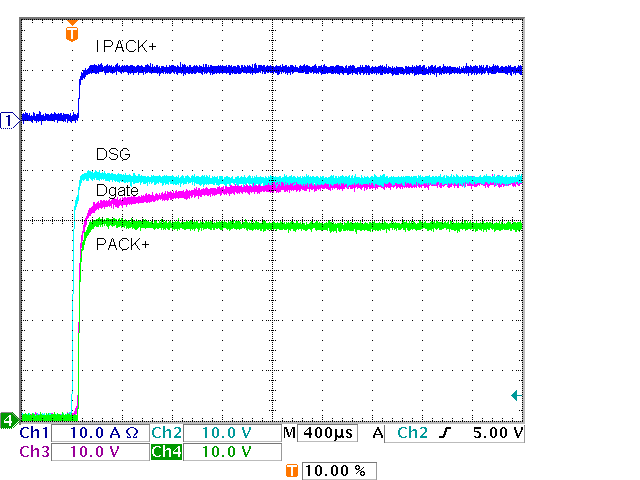
[picture p44: Documents/images/sluaan9a-072.png]
Рис. 8-10. DSG Увімк., 8 FET, 10 кОм, 470 нФ


*Рис. 8-10. DSG Увімк., 8 FET, 10 кОм, 470 нФ*

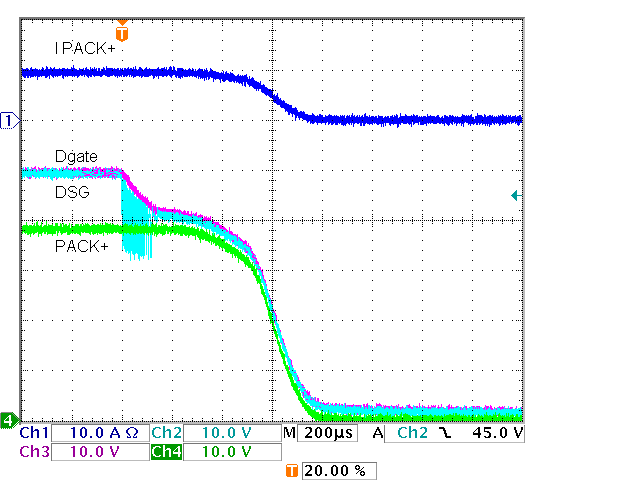
[picture p45: Documents/images/sluaan9a-074.png]
Рис. 8-11. DSG Вимк., 8 FET, R41 1 кОм


*Рис. 8-11. DSG Вимк., 8 FET, R41 1 кОм*

Менший резистор відтягування для DSG, який міг бути невідповідним для меншої кількості FET, збільшить час вимкнення для більшої кількості FET. На Рис. 8-12 та Рис. 8-13 R41 повертається до 100 Ом. Ввімкнення не змінюється, але вимкнення є швидшим. Перемикання 12 FET з такою конфігурацією показано на Рис. 8-14 та Рис. 8-15.

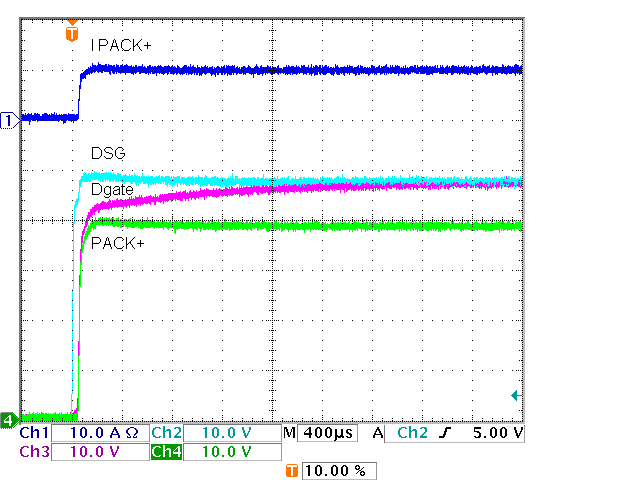
[picture p46: Documents/images/sluaan9a-076.png]
Рис. 8-12. DSG Увімк., 8 FET, 10 кОм, 470 нФ


*Рис. 8-12. DSG Увімк., 8 FET, 10 кОм, 470 нФ*

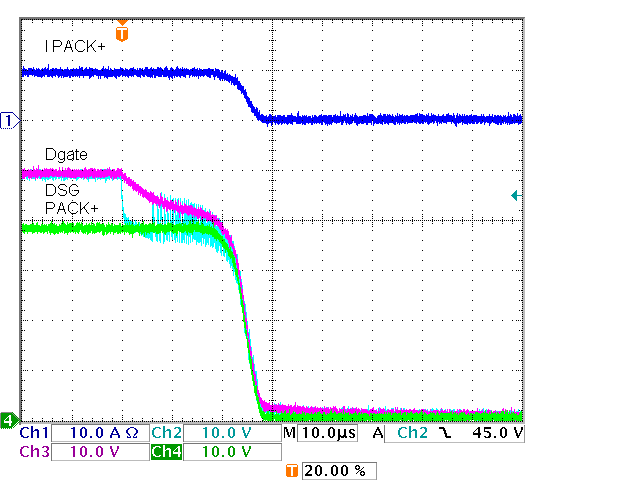
[picture p47: Documents/images/sluaan9a-078.png]
Рис. 8-13. DSG Вимк., 8 FET, R41 100 Ом


*Рис. 8-13. DSG Вимк., 8 FET, R41 100 Ом*

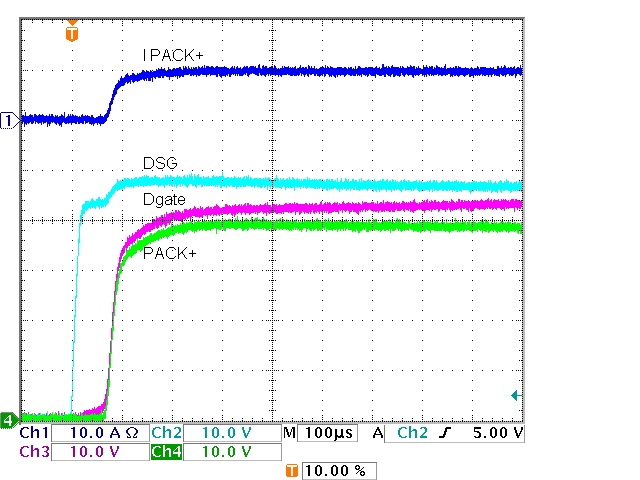
[picture p48: Documents/images/sluaan9a-080.png]
Рис. 8-14. DSG Увімк., 12 FET, 10 кОм, 470 нФ


*Рис. 8-14. DSG Увімк., 12 FET, 10 кОм, 470 нФ*

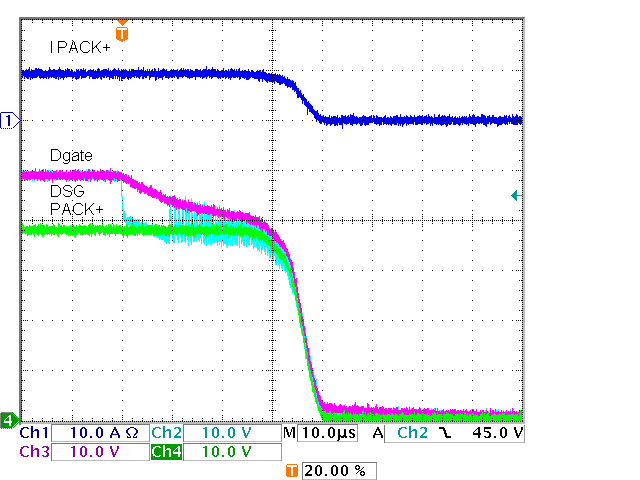
[picture p49: Documents/images/sluaan9a-082.png]
Рис. 8-15. DSG Вимк., 12 FET, R41 100 Ом


*Рис. 8-15. DSG Вимк., 12 FET, R41 100 Ом*

При заданому опорі відтягування затвора, додавання FET збільшує ємність та уповільнює початковий перепад виводу DSG через його внутрішній опір та перехід затвора. Ефект важко ідентифікувати разом із перехідним процесом PACK+. У наведеній нижче таблиці показано типові значення, зібрані для різної кількості FET з підключеним PACK+ до BAT+ при R41 = 100 Ом. Часи спадання від 90% до 10%, вимірювався приклад затвора FET, а не сітка Dgate.

**Таблиця 8-1. Часи спадання для різної кількості FET, 100 Ом**

| Кількість FET | Сума Ciss, нФ | Початковий час спадання DSG, мкс | Час спадання затвора прикладного FET, мкс |
|:---:|:---:|:---:|:---:|
| 1 | 9,25 | 0,50 | 6,4 |
| 2 | 18,5 | 1,0 | 9,6 |
| 4 | 37 | 1,4 | 16 |
| 6 | 55,5 | 2,3 | 21 |
| 8 | 74 | 5,0 | 27 |
| 10 | 92,5 | 6,7 | 33 |
| 12 | 111 | 7,2 | 39 |

На наведених вище зображеннях вивід DSG розряджає затворну ємність безпосередньо. PNP-транзистор може бути використаний для розряду затворної ємності з управлінням від виводу DSG, як показано на Рис. 5-2. На Рис. 8-16 та Рис. 8-17 показано ввімкнення та вимкнення з 12 FET розряду та цією схемою.

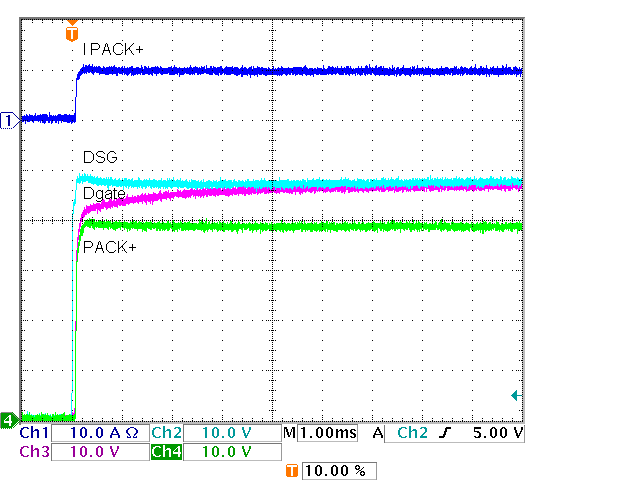
[picture p50: Documents/images/sluaan9a-084.png]
Рис. 8-16. DSG Увімк., 12 FET, 10 кОм, PNP, 470 нФ


*Рис. 8-16. DSG Увімк., 12 FET, 10 кОм, PNP, 470 нФ*

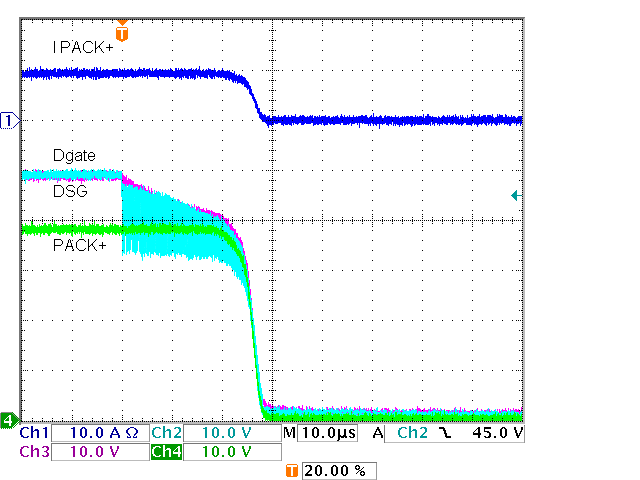
[picture p51: Documents/images/sluaan9a-086.png]
Рис. 8-17. DSG Вимк., 12 FET, R41 1 кОм, PNP


*Рис. 8-17. DSG Вимк., 12 FET, R41 1 кОм, PNP*

Читач, мабуть, помітив, що час ввімкнення зростає зі збільшенням кількості FET. Це пов'язано з опором 10 кОм (R40, R45) для підтримання потужності в резисторах на розумному рівні при зворотному заряді. Якщо схема зворотного заряду не потрібна, DSG може бути підключений до загальної точки затвора через один резистор, замінюючи мережу з'єднань Рис. 5-1. Діоди Шоттки, R40 та R45, транзистор фіксатора зворотного заряду та пов'язані компоненти пропускаються. Дивіться Рис. 8-18. Перемикання показано на Рис. 8-19 та Рис. 8-20.

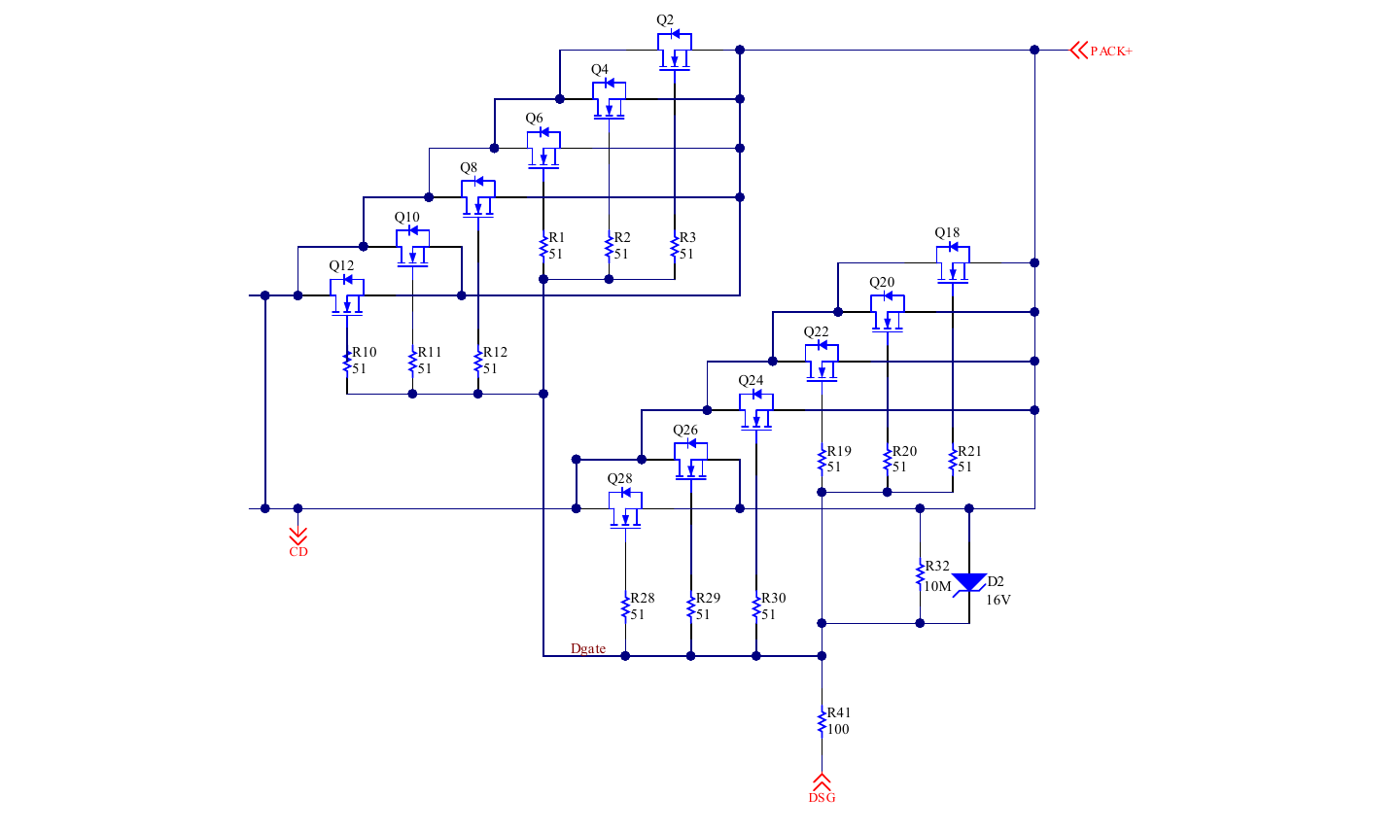
[picture p52: Documents/images/sluaan9a-fig8-18.png]
Рис. 8-18. Управління DSG без схеми захисту від зворотної зарядки


*Рис. 8-18. Управління DSG без схеми захисту від зворотної зарядки*

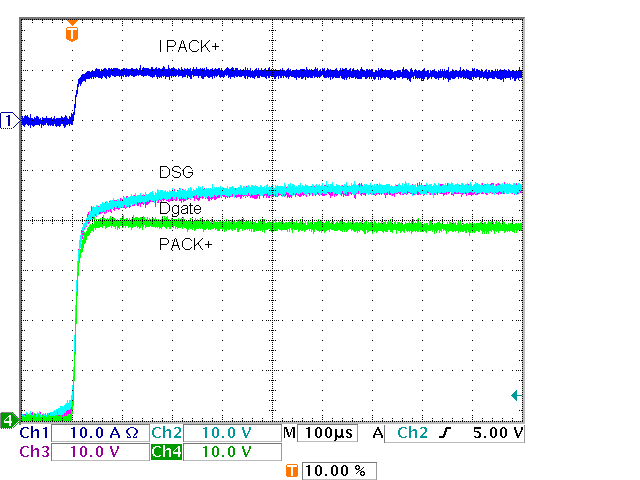
[picture p53: Documents/images/sluaan9a-088.png]
Рис. 8-19. DSG Увімк., 12 FET, 100 Ом, без схеми зворотного заряду, 470 нФ


*Рис. 8-19. DSG Увімк., 12 FET, 100 Ом, без схеми зворотного заряду, 470 нФ*

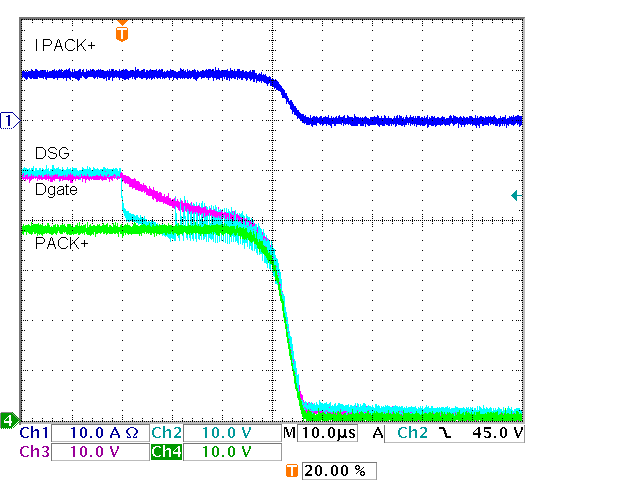
[picture p54: Documents/images/sluaan9a-090.png]
Рис. 8-20. DSG Вимк., 12 FET, 100 Ом, без схеми зворотного заряду


*Рис. 8-20. DSG Вимк., 12 FET, 100 Ом, без схеми зворотного заряду*

Якщо схема зворотного заряду потрібна, P-канальний FET може бути встановлений замість R45 з затвором, прив'язаним до виводу LD, як показано на Рис. 8-21. FET буде увімкненим, коли DSG піднімається; при падінні DSG до LD FET вимикається, і R40 допоможе розряджати затворну ємність FET розряду, але вимкнеться, дозволяючи резистору відтягування затвора R41 завершити вимкнення. На Рис. 8-22 та Рис. 8-23 R40 = 1 кОм. При вимкненому DSG P-канальний FET Q32 вимкнений, і зворотна напруга зарядки знизить сітку Dgate без потоку струму через R40. При ввімкненні R40 діятиме разом із затворною ємністю і може бути підібраний так, щоб Dgate краще відповідала виводу DSG. Пам'ятайте, що струм ввімкнення надходить від конденсатора CP1, і просідання DSG залежатиме від внутрішнього опору та передачі заряду від конденсатора CP1 до затворів FET. Цей приклад використовує конденсатор CP1 470 нФ, і знижену напругу після ввімкнення можна спостерігати. При вимкненні R40 паралельний шляху R41 та Шоттки до тих пір, поки напруга не стане достатньо низькою для вимкнення P-канального FET. Слід зазначити, що BQ769x2 не обмежує напругу між DSG та LD при ввімкненні. Мета P-канальної схеми — дозволити використання малого R40, щоб затвори FET, PACK+ та LD швидко піднімалися разом з DSG. Якщо використовується великий R40, або ввімкнення FET розряду є повільним, бажаний стабілітрон на з'єднанні джерело-затвор і великий резистор від затвора Q32 до з'єднання LD для захисту затвора Q32.

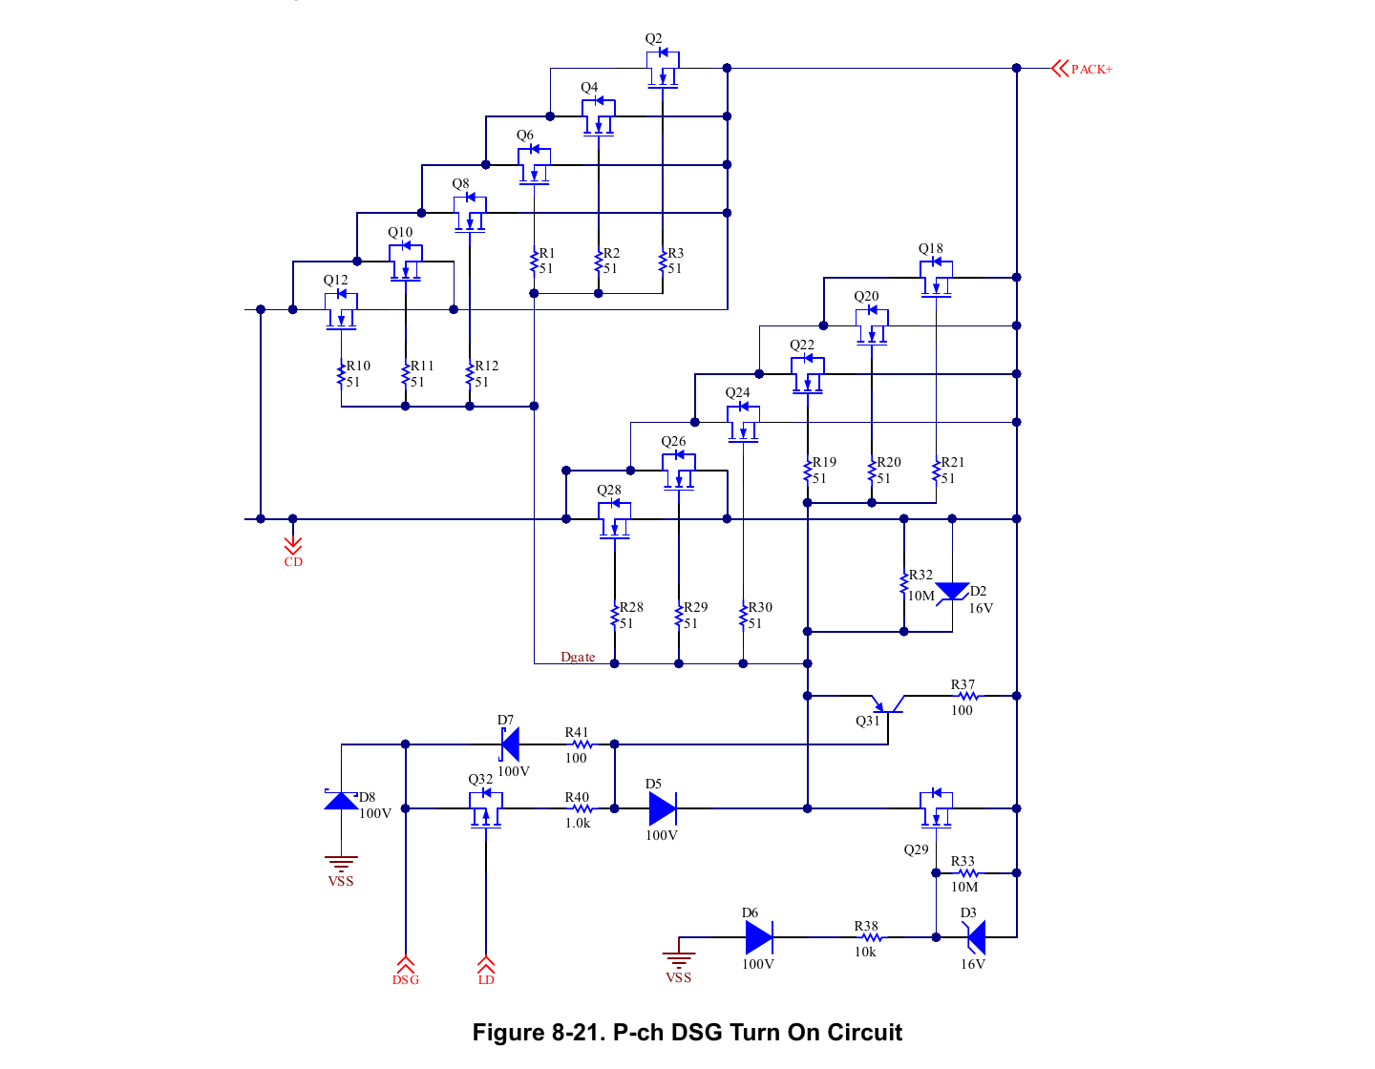
[picture p55: Documents/images/sluaan9a-fig8-21.png]
Рис. 8-21. Схема ввімкнення DSG P-ch


*Рис. 8-21. Схема ввімкнення DSG P-ch*

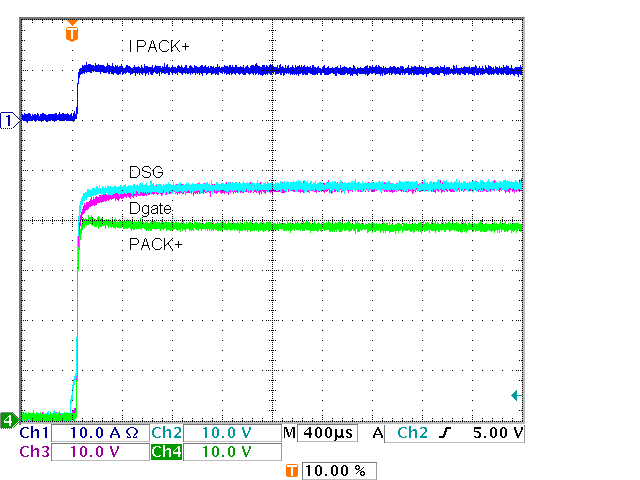
[picture p56: Documents/images/sluaan9a-092.png]
Рис. 8-22. DSG Увімк., 12 FET, P-ch, шлях ввімкнення 1 кОм, 470 нФ


*Рис. 8-22. DSG Увімк., 12 FET, P-ch, шлях ввімкнення 1 кОм, 470 нФ*

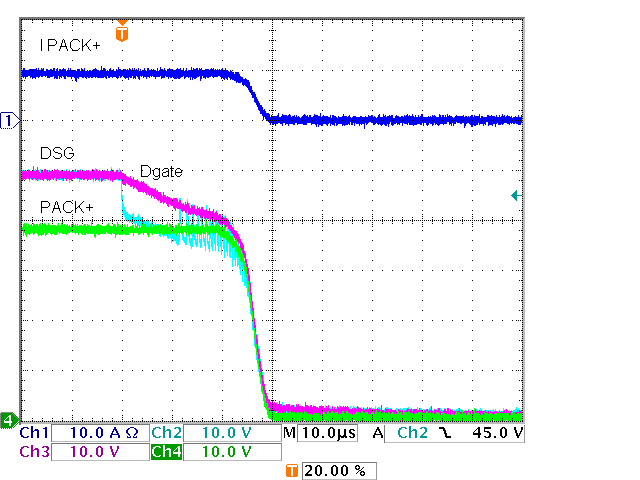
[picture p57: Documents/images/sluaan9a-094.png]
Рис. 8-23. DSG Вимк., 12 FET, P-ch, шлях ввімкнення 1 кОм, 100 Ом


*Рис. 8-23. DSG Вимк., 12 FET, P-ch, шлях ввімкнення 1 кОм, 100 Ом*

Приклад короткого замикання показано на Рис. 8-24 з одним FET і кількома кОм для R41. При виникненні короткого замикання BAT+ та PACK+ утримуються разом FET та притягуються вниз навантаженням. Розряд виводу BAT блокується конденсатором виводу BAT, а конденсатор CP1 утримує напругу зарядового насоса вище нього як джерело живлення для виходів CHG та DSG. Затвори FET заряду та розряду захищені D1 та D2 у Рис. 5-1. CHG та DSG завантажуються і дещо просідають через їх внутрішній опір, але більша частина напруги падає на резистори до затворів: R44, R40 та R45. Напруга DSG впаде, оскільки подія короткого замикання вимірюється за часом. При більших затримках SCD та менших резисторах затворів CHG та DSG впадуть до тих пір, поки D1 та D2 не перестануть проводити. BQ769x2 відраховує час події за допомогою джерела живлення REG18. Коли вибрана затримка спрацьовує, DSG вимикається, як описано раніше. R41 вимикає FET розряду і має бути вибраний таким чином, щоб вимикати FET достатньо швидко для уникнення надмірного нагрівання і достатньо повільно для уникнення надмірного підвищення BAT+.

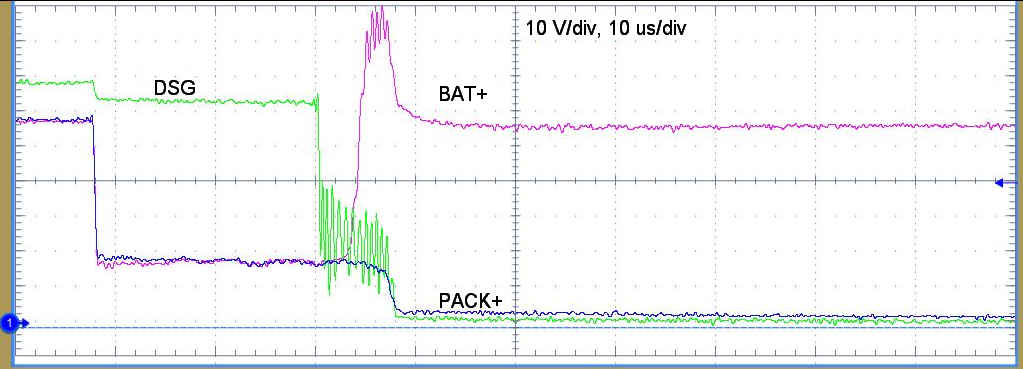
[picture p58: Documents/images/sluaan9a-096.png]
Рис. 8-24. Приклад короткого замикання


*Рис. 8-24. Приклад короткого замикання*

---

## 9 Шляхи струму драйвера DSG

Як і драйвер CHG, сила драйвера DSG є поширеним питанням, але також не має простої відповіді. Драйвер був розроблений для забезпечення керованого ввімкнення та вимкнення FET із навантажувальною ємністю. Він не оцінюється в амперах, як деякі драйвери затворів загального призначення, і не характеризується опором, але характеризується часами наростання та спадання, показаними в паспорті даних. При ввімкненні DSG струм тече від конденсатора CP1 через вивід DSG до затворів FET, як показано на Рис. 9-1. Вимірювання при малому струмі може показати внутрішній опір приблизно 2 кОм, але перемикач не є лінійним і обмежуватиме струм. Зарядовий насос забезпечує обмежений струм, тому струм для заряду затворів FET надходить від конденсатора CP1 — C15, і розподіляє заряд від конденсатора CP1 до ємностей конденсатора та затворів. При заряді затворної ємності FET розряду Q5 вмикається, і навантаження заряджається, тому конденсатору CP1 не потрібно заряджати навантажувальну ємність. Більший конденсатор CP1 допустить менше просідання при ввімкненні, як було показано раніше для ввімкнення драйвера CHG. Знову ж таки, струм від конденсатора CP1 C15 підтримується C12 та поповнюється струмом через D1 та R11.

Читач повинен зауважити, що якщо FET заряду Q2 вимкнений — як, наприклад, при перебуванні BQ769x2 у режимі SLEEP через відсутність навантажувального струму, — R26 підніме напругу PACK+ приблизно до напруги зарядового насоса. Таким чином, незавантажений акумуляторний блок із BQ769x2 у режимі SLEEP може показати напругу PACK+ вище напруги батареї.

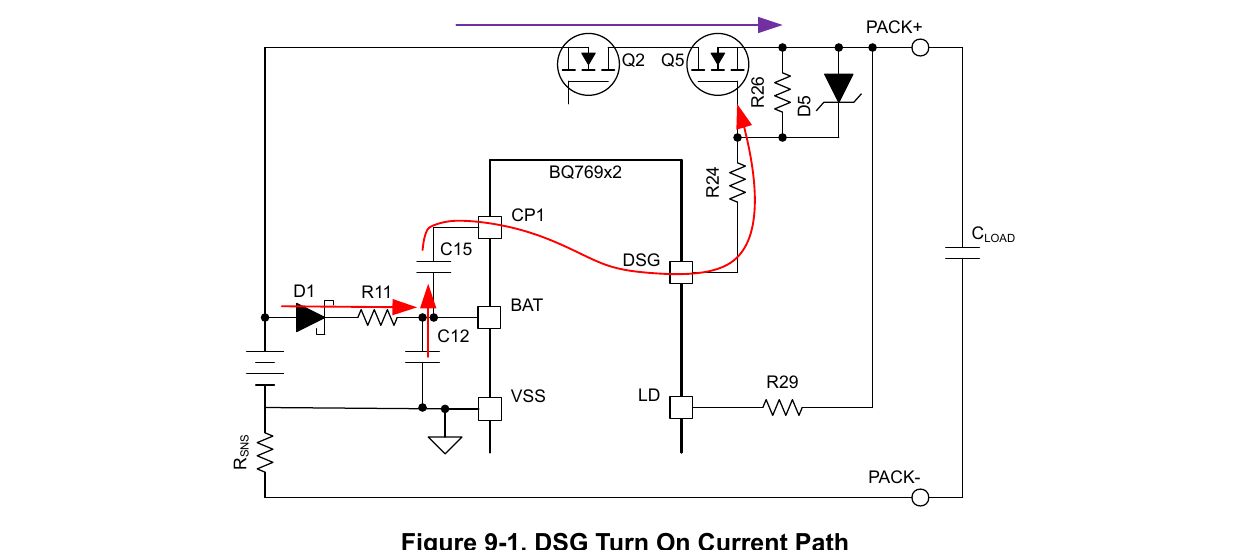
[picture p59: Documents/images/sluaan9a-fig9-1.png]
Рис. 9-1. Шлях струму ввімкнення DSG


*Рис. 9-1. Шлях струму ввімкнення DSG*

Типовий рекомендований резистор затвор-джерело (R26) становить 10 МОм, забезпечуючи навантаження приблизно 1,1 мкА при роботі зарядового насоса на рівні $V_{(FETON\_HI)}$. Хоча будь-яке навантаження спричинить деяке просідання напруги зарядового насоса, зарядовий насос зазвичай може підтримувати 10 В при навантаженні на драйвери приблизно до 40 мкА. Зарядовий насос спільний із драйвером CHG, тому його навантаження також слід враховувати. При завантаженні драйвера DSG його напруга впаде, що також призведе до падіння напруги на виводі CHG, якщо CHG також увімкнений. Зарядовий насос може подавати приблизно 200 мкА у заземлений резистор затвор-джерело при напрузі BAT+. Однак при заземленому резисторі затвор-джерело FET розряду буде вимкнений, і напруга PACK+ швидше за все впаде через навантаження. При відтягуванні DSG нижче рівня BAT+ додатковий струм потече через вивід DSG від виводу BAT. Цей струм є обмеженим; приклад показано на Рис. 9-2. При реалізації схеми для перевизначення виводу DSG слід передбачити деякий запас вище обмеження струму, щоб переконатись, що FET розряду вимкнений і не працює як повторювач джерела. Також враховуйте відтягування CHG: знижена напруга залишить FET заряду вимкненим. Може бути корисним сигналізувати вимкнення виходу CHG FET через вхід CFETOFF мікросхеми BQ769x2, де це доступно.

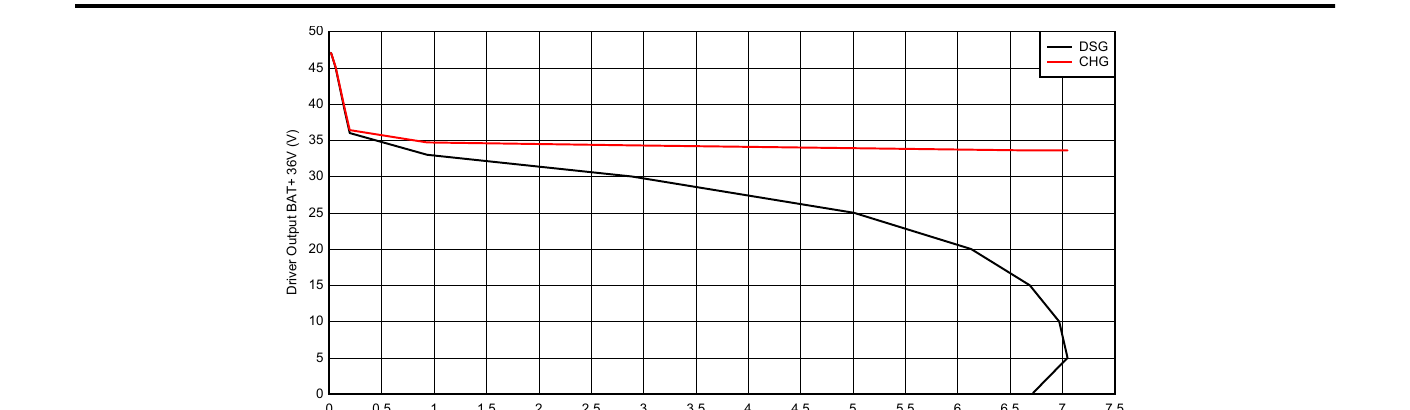
[picture p60: Documents/images/sluaan9a-fig9-2.png]
Рис. 9-2. DSG під навантаженням при батареї 36 В


*Рис. 9-2. DSG під навантаженням при батареї 36 В*

Коли драйвер DSG вимикається, струм відбирається від виводу DSG до виводу VSS, і Ciss FET розряду розряджається, як показано на Рис. 9-3. Спочатку цей струм складає приблизно 70 мА. Коли DSG падає до рівня виводу LD, струм переривається і імпульсується протягом типових 150 мкс, показаних у розділі FET Driver Turn-Off паспорту даних. Після закінчення часу очікування навантаження знижується приблизно до 1 мА, але все ще спадає, оскільки напруга виводу DSG наближається до рівня виводу LD. Цей метод вимикає FET розряду без спроби виводу DSG швидко розрядити $C_{LOAD}$. Резистор виводу DSG $R_{GATE}$ (R24 окремо або в комбінації з R25) не рекомендується нижче 100 Ом для забезпечення деякої ізоляції виводу від шляху струму.

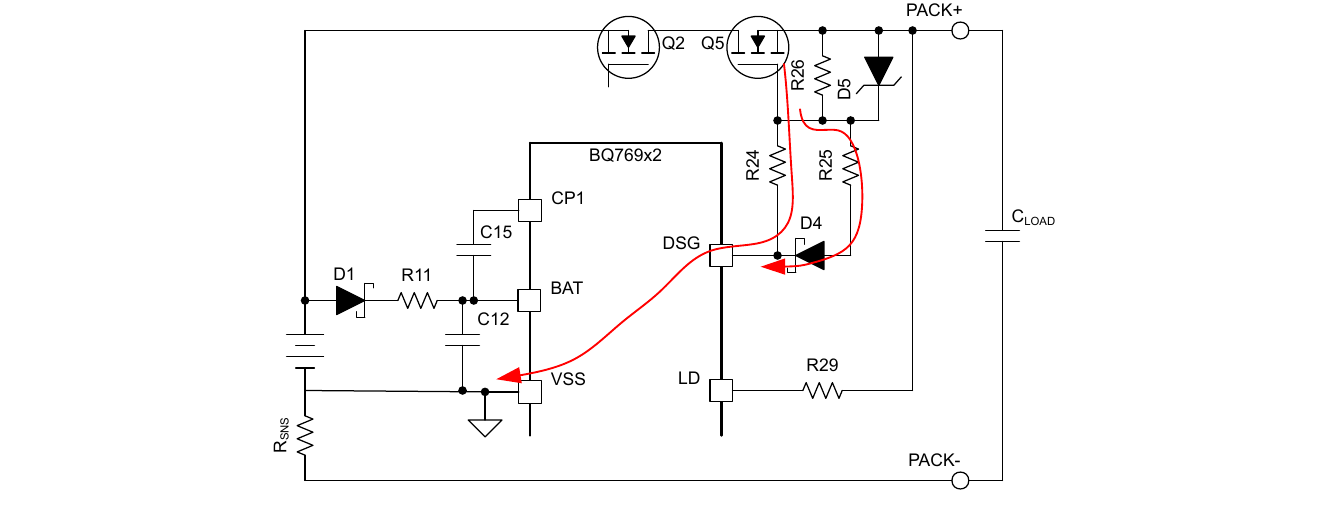
[picture p61: Documents/images/sluaan9a-fig9-3.png]
Рис. 9-3. Шлях струму вимикання DSG


*Рис. 9-3. Шлях струму вимикання DSG*

---

## 10 Висновок

Пристрої сімейства BQ76952 забезпечують управління FET з боку високої напруги і можуть використовуватися в конфігураціях з кількома FET. Розміряйте конденсатор CP1 для допустимого просідання при ввімкненні FET. Вибирайте резистори у з'єднаннях виводів CHG та DSG до затвора для відповідного ввімкнення та вимкнення FET. За необхідності передбачайте допоміжні схеми вимкнення або ввімкнення, що відповідають вимогам прикладної системи. Схеми та результати тестів, представлені в цьому документі, допоможуть розробнику розпізнати умови для розгляду у своїй конструкції. Зверніться до паспортів даних та технічних довідкових посібників для отримання інформації про пристрій та конфігурацію.

---

## 11 Посилання

- Texas Instruments, *BQ76952 3S-16S Battery Monitor and Protector Data Sheet*
- Texas Instruments, *BQ769142 3S-14S Battery Monitor and Protector Data Sheet*
- Texas Instruments, *BQ76942 3S-10S Battery Monitor and Protector Data Sheet*
- Texas Instruments, *BQ76952 Technical Reference Manual*
- Texas Instruments, *BQ769142 Technical Reference Manual*
- Texas Instruments, *BQ76942 Technical Reference Manual*
- Texas Instruments, *BQ76952EVM User's Guide*
- Texas Instruments, *BQ76942EVM User's Guide*
- Texas Instruments, *CSD19536KCS 100-V, N-Channel NexFET™ Power MOSFET*

---

## 12 Історія ревізій

*Примітка: Номери сторінок у попередніх ревізіях можуть відрізнятися від номерів сторінок у поточній версії.*

**Зміни від Ревізії \* (Вересень 2020) до Ревізії A (Березень 2022)**

| | Зміна | Стор. |
|---|---|---|
| • | Змінено назву та анотацію для спрощення заголовку | 1 |
| • | Додано розділ про компоненти схеми зворотного заряду | 5 |
| • | Змінено підпис до Рис. 6-14 | 10 |
| • | Додано розділ про потік струму CHG | 14 |
| • | Змінено опис роботи виводу DSG | 17 |
| • | Додано розділ про потік струму DSG | 25 |
| • | Додано посилання на документи BQ769142 | 28 |
