LVladymyr/WAFEL-Evaluation-Board/Documents/4_References/SLUAA09A Translation.md

# Кілька FET разом з моніторами акумуляторів BQ7694204
*Прикладна нотатка (Application Note) — Texas Instruments SLUAA09A*
*Willy Massoth — Вересень 2020 / Переглянуто березень 2022*

---

## Анотація

Типові схеми для сімейства моніторів акумуляторів BQ7694204 (яке включає BQ7694204, BQ76942 та BQ769142) показують одиничні послідовні FET з боку високої напруги. Багато розробників потребують паралельного з'єднання FET у своїх конструкціях для підвищення струмової здатності або розсіювання тепла. Цей документ обговорює та демонструє результати комутації кількох FET з використанням пристроїв BQ7694204 і надає приклад для розробників, що реалізують кілька FET з цим або іншими пристроями сімейства BQ7694204.

---

## Зміст

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

---

## 1 Вступ

Типова акумуляторна батарея має один набір клем як для заряду, так і для розряду. Струм проходить через FET заряду та розряду, з'єднані послідовно. Оскільки струм тече через обидва FET, їх розміри і кількість для заряду та розряду однакові. Сімейство моніторів акумуляторів BQ7694204, що складається з BQ76942 та BQ7694204, підтримує послідовні FET з боку високої напруги. Посилання на BQ7694204 у цьому документі, як правило, поширюються на всіх членів сімейства, якщо не зазначено інше. Типова схема з BQ76942 і послідовними FET показана на Рис. 1-1. Схема розрахована на реалізацію з 7 елементами та включає FET попереднього заряду та попереднього розряду. Шлях попереднього заряду використовується для обмеження струму в батарею від зарядного пристрою з фіксованою напругою при глибокому розряді батареї. Шлях попереднього розряду використовується для заряду ємнісних навантажень без стрибка великого струму. При використанні послідовних FET існує можливість заряду через вимкнений FET розряду або розряду через вимкнений FET заряду. Струм через захисний діод вимкненого FET може виробляти значну кількість тепла, тому пристрої BQ7694204 використовують функцію захисту тілесного діода для ввімкнення FET, коли струм тече в незахищеному напрямку.

Рис. 1-1. Типова схема FET послідовної 7S-серії

![[../Assets/Pasted image 20260403155612.png]]

*Рис. 1-1. Типова схема FET послідовної 7S-серії*

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

---

## 2 Схема захисту від зворотної зарядки

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

Рис. 2-1. Negative PACK+ без схеми захисту від зворотної зарядки

*Рис. 2-1. Negative PACK+ без схеми захисту від зворотної зарядки*

Рис. 2-2. Negative PACK+ зі схемою захисту від зворотної зарядки

*Рис. 2-2. Negative PACK+ зі схемою захисту від зворотної зарядки*

---

## 3 Вибір компонентів захисту від зворотної зарядки

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

Рис. 3-1. Шляхи струму при зворотному заряді
![[../Assets/Pasted image 20260403140707.png]]

*Рис. 3-1. Шляхи струму при зворотному заряді*

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

Резистор виводу LD R29 повинен мати значення, рекомендоване в паспорті даних. При використанні резисторів із низьким номіналом потужності слід вибрати послідовну або паралельну комбінацію резисторів для досягнення потрібного опору та відповідного розсіювання потужності, коли PACK+ перебуває на найнижчому рівні. D6 запобігає протіканню струму та порушенню обмеження ABS MAX для виводу LD мікросхеми BQ7694204.

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

---

## 4 Зарядовий насос та ввімкнення FET

BQ7694204 використовує зарядовий насос для забезпечення напруги, що перевищує напругу батарея+, для ввімкнення N-канальних MOSFET з боку високої напруги, що використовуються в системі. Летючий конденсатор зарядового насоса є внутрішнім, заряд зберігається у зовнішньому конденсаторі CP1 пристрою. CP1 є джерелом живлення для драйверів CHG та DSG. На Рис. 4-1 — 4-4 BQ7694204 переведений у режим SHUTDOWN та пробуджується сигналом TS2. Коли зарядовий насос досягає напруги, він вимикається до тих пір, поки його напруга не впаде, і потім запускається знову. Часто можна побачити пульсацію на напрузі CP1 — повільне падіння з наступним швидким підйомом. На Рис. 4-1 зверніть увагу на повільне циклування перед ввімкненням FET та більш швидку пульсацію після ввімкнення FET з доданим навантаженням резисторів R_GS та навантаженням додаткових щупів осцилографа. На Рис. 4-2 показано більш детально нарощування зарядового насоса при низькій напрузі. Час наростання є більшим при нормальній напрузі, показаній на Рис. 4-3. Використання більшого конденсатора CP1 також збільшує час наростання, як на Рис. 4-4. Зверніть увагу, що зарядовий насос все ще перебуває в перехідному процесі, коли FET вмикаються. Використання конденсатора CP1 більше 2,2 мкФ не рекомендується з пристроями сімейства BQ7694204.

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

*Рис. 4-1. Запуск зарядового насоса і ввімкнення FET, низька напруга, 470 нФ*

Рис. 4-2. Запуск зарядового насоса, низька напруга, 470 нФ

*Рис. 4-2. Запуск зарядового насоса, низька напруга, 470 нФ*

Рис. 4-3. Запуск зарядового насоса, нормальна напруга, 470 нФ

*Рис. 4-3. Запуск зарядового насоса, нормальна напруга, 470 нФ*

Рис. 4-4. Запуск зарядового насоса і ввімкнення FET, CP1 2 мкФ

*Рис. 4-4. Запуск зарядового насоса і ввімкнення FET, CP1 2 мкФ*

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

$$Q = V_1 \times C_{CP1} = V_2 \times (C_{CP1} + N \times C_{iss}) \tag{1}$$

Тоді напруга після ввімкнення буде пропорцією початкової напруги:

$$V_2 = V_1 \times C_{CP1} / (C_{CP1} + N \times C_{iss}) \tag{2}$$

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

Рис. 4-5. Просідання CP1, 24 FET, C_CP1 470 нФ

*Рис. 4-5. Просідання CP1, 24 FET, $C_{CP1}$ 470 нФ*

Рис. 4-6. Просідання CP1, 24 FET, C_CP1 2 мкФ

*Рис. 4-6. Просідання CP1, 24 FET, $C_{CP1}$ 2 мкФ*

---

## 5 Тестові схеми з паралельними FET

Коли FET працюють паралельно, вони можуть осцилювати при перемиканні. У індивідуальному шляху затвора часто використовується невеликий опір або феритова намистина для запобігання осциляції. На Рис. 5-1 показана тестова схема з кількома FET. Резистори 51 Ом використовуються в тестових схемах цього прикладного звіту для ізоляції окремих затворів від загальних ліній Cgate та Dgate. Cgate та Dgate зазвичай використовуються на рисунках у цьому документі, а не індивідуальна напруга затвора, якщо не зазначено інше. При використанні одного FET резистор 51 Ом залишається. FET заповнюються за необхідністю, решта схеми BQ7694204 залишається незмінною. FET CSD19536KCS, що використовуються в цій прикладній нотатці, мають типове значення Ciss 9,25 нФ. R41 та R44 регулюються залежно від кількості FET. Схема захисту від зворотного заряду збережена у тестових схемах з паралельними FET, Q29 є фіксуючим FET.

Рис. 5-1. Тестова схема з кількома FET

![[../Assets/Pasted image 20260402193022.png]]

*Рис. 5-1. Тестова схема з кількома FET*

BQ7694204 має внутрішні опори драйверів, тому для більших навантажень можна використовувати локальну схему вимкнення. На Рис. 5-2 показана схема, в якій PNP-транзистори використовуються для забезпечення локального контуру струму для вимкнення FET. Це дозволяє вимикати з меншим локальним контуром через транзистор і зовнішній опір. При вимиканні FET заряду CHG відбирає базовий струм від Q30 через R44, тоді як колекторний струм розряджає затвори FET заряду через R35. Аналогічно DSG відбирає базовий струм для Q31 через комбінацію R40, R45, R41 та D7. Колекторний струм розряджає затвори FET через R37. Ввімкнення все ще відбувається від конденсатора зарядового насоса через D4 для CHG та D5 для DSG. Якщо падіння напруги на D4 та D5 є проблемою, можна використовувати діод Шоттки або додати великий паралельний резистор для підняття затворів до повної напруги після початкового стрибка струму.

Рис. 5-2. Тестова схема з кількома FET з локальними контурами струму
![[../Assets/Pasted image 20260403140523.png]]

*Рис. 5-2. Тестова схема з кількома FET з локальними контурами струму*

---

## 6 Драйвер CHG

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

Рис. 6-1. CHG Увімк., 1 FET, 5,1 кОм, 470 нФ

*Рис. 6-1. CHG Увімк., 1 FET, 5,1 кОм, 470 нФ*

Рис. 6-2. CHG Вимк., 1 FET, 5,1 кОм

*Рис. 6-2. CHG Вимк., 1 FET, 5,1 кОм*

Рис. 6-3. CHG Увімк., 2 FET, 5,1 кОм, 470 нФ

*Рис. 6-3. CHG Увімк., 2 FET, 5,1 кОм, 470 нФ*

Рис. 6-4. CHG Вимк., 2 FET, 5,1 кОм

*Рис. 6-4. CHG Вимк., 2 FET, 5,1 кОм*

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

Рис. 6-5. CHG Увімк., 1 FET, 1 кОм, 470 нФ

*Рис. 6-5. CHG Увімк., 1 FET, 1 кОм, 470 нФ*

Рис. 6-6. CHG Вимк., 1 FET, 1 кОм

*Рис. 6-6. CHG Вимк., 1 FET, 1 кОм*

Рис. 6-7. CHG Увімк., 1 FET, 100 Ом, 470 нФ

*Рис. 6-7. CHG Увімк., 1 FET, 100 Ом, 470 нФ*

Рис. 6-8. CHG Вимк., 1 FET, 100 Ом

*Рис. 6-8. CHG Вимк., 1 FET, 100 Ом*

При більшій кількості FET перемикання уповільнюється, оскільки опір діє на затворну ємність. На Рис. 6-9 показано вимкнення 4 FET при R44 = 100 Ом. Для більш швидкого перемикання локальний контур струму, створений PNP-транзистором, керованим виводом CHG мікросхеми BQ7694204, показаний на Рис. 5-2, дозволяє затвору розряджатися через менший опір для більш швидкого переходу, як показано на Рис. 6-10. R44 залишається рівним 100 Ом для цього прикладу.

Рис. 6-9. CHG Вимк., 4 FET, 100 Ом

*Рис. 6-9. CHG Вимк., 4 FET, 100 Ом*

Рис. 6-10. CHG Вимк., 4 FET, 100 Ом, PNP

*Рис. 6-10. CHG Вимк., 4 FET, 100 Ом, PNP*

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

Рис. 6-11. CHG Вимк., 8 FET, 100 Ом

*Рис. 6-11. CHG Вимк., 8 FET, 100 Ом*

Рис. 6-12. CHG Вимк., 8 FET, 5,1 кОм, PNP

*Рис. 6-12. CHG Вимк., 8 FET, 5,1 кОм, PNP*

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

*Рис. 6-13. CHG Увімк., 8 FET, 5,1 кОм, PNP, 470 нФ*

Рис. 6-14. CHG Увімк., 8 FET, 100 Ом, PNP, 470 нФ

*Рис. 6-14. CHG Увімк., 8 FET, 100 Ом, PNP, 470 нФ*

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

Рис. 6-15. CHG Увімк., 8 FET, 100 Ом, PNP, 470 нФ

*Рис. 6-15. CHG Увімк., 8 FET, 100 Ом, PNP, 470 нФ*

Рис. 6-16. CHG Увімк., 8 FET, 100 Ом, PNP, 2 мкФ

*Рис. 6-16. CHG Увімк., 8 FET, 100 Ом, PNP, 2 мкФ*

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

Рис. 6-17. CHG Увімк., 12 FET, 100 Ом, PNP, 2 мкФ

*Рис. 6-17. CHG Увімк., 12 FET, 100 Ом, PNP, 2 мкФ*

Рис. 6-18. CHG Вимк., 12 FET, 100 Ом, PNP

*Рис. 6-18. CHG Вимк., 12 FET, 100 Ом, PNP*

---

## 7 Шляхи струму драйвера CHG

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

Рис. 7-1. Шлях струму ввімкнення драйвера CHG

*Рис. 7-1. Шлях струму ввімкнення драйвера CHG*

Коли BQ7694204 перебуває в режимі SHUTDOWN, вивід CHG може опускатись до VSS. Однак у нормальній схемі стабілітрон затвор-джерело FET заряду D2 та резистор R15 утримуватимуть напругу виводу CHG на рівні напруги батареї.

Типовий рекомендований резистор затвор-джерело (R15) становить 10 МОм, забезпечуючи навантаження приблизно 1,1 мкА при роботі зарядового насоса на рівні $V_{(FETON\_HI)}$. Хоча будь-яке навантаження спричинить деяке просідання напруги зарядового насоса, зарядовий насос зазвичай може підтримувати 10 В при навантаженні на драйвери приблизно до 40 мкА. Зарядовий насос спільний із драйвером DSG, тому його навантаження також слід враховувати. При завантаженні драйвера CHG його напруга впаде, що також призведе до падіння напруги на виводі DSG, якщо DSG також увімкнений. Приклад показано на Рис. 7-2. Зарядовий насос може подавати приблизно 200 мкА у заземлений резистор затвор-джерело. Там є коефіцієнт посилення по потоку приблизно 6, тому струм виводу BAT збільшиться приблизно на 1200 мкА для забезпечення 200 мкА до CHG. Коли драйвер CHG відтягується нижче, він впаде нижче напруги виводу BAT, і струм обмежуватиметься. При реалізації схеми для перевизначення виводу CHG слід передбачити деякий запас вище можливостей зарядового насоса, щоб переконатись у вимиканні FET заряду. Також враховуйте відтягування DSG: знижена напруга залишить FET розряду у режимі повторювача джерела. Може бути корисним сигналізувати вимкнення виходу DSG FET через вхід DFETOFF мікросхеми BQ7694204, де це доступно.

Рис. 7-2. CHG під навантаженням при батареї 36 В

*Рис. 7-2. CHG під навантаженням при батареї 36 В*

Коли драйвер CHG вимикається, CHG підтягується до виводу BAT, і Ciss FET заряду розряджається до ємності виводу BAT C12, як показано на Рис. 7-3. Відтягування виглядатиме приблизно як 1 кОм, але буде варіюватися залежно від напруги. Це може тимчасово підвищити напругу на виводі BAT до тих пір, поки струм навантаження BQ7694204 не знизить напругу BAT до нормального рівня. Приклад підйому виводу BAT при вимиканні з 4 FET показано на Рис. 7-4. C12 не слід робити меншим за типовий 1 мкФ для запобігання підвищенню напруги BAT. Використання локальної схеми контуру струму зменшить струм, що надходить до C12, і результуючий підйом напруги, крім прискорення вимкнення FET заряду, як показано у порівнянні між Рис. 6-9 та Рис. 6-10.

Рис. 7-3. Шлях струму вимикання драйвера CHG

*Рис. 7-3. Шлях струму вимикання драйвера CHG*

Рис. 7-4. CHG Вимк., 4 FET, 100 Ом, без струму

*Рис. 7-4. CHG Вимк., 4 FET, 100 Ом, без струму*

---

## 8 Драйвер DSG

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

Рис. 8-1. DSG Увімк., 1 FET, 10 кОм, 470 нФ

*Рис. 8-1. DSG Увімк., 1 FET, 10 кОм, 470 нФ*

Рис. 8-2. DSG Вимк., 1 FET, R41 100 Ом

*Рис. 8-2. DSG Вимк., 1 FET, R41 100 Ом*

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

Рис. 8-3. Перехідний процес батареї, 1 FET, R41 100 Ом

*Рис. 8-3. Перехідний процес батареї, 1 FET, R41 100 Ом*

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

Рис. 8-4. DSG Увімк., 1 FET, 10 кОм, 470 нФ

*Рис. 8-4. DSG Увімк., 1 FET, 10 кОм, 470 нФ*

Рис. 8-5. DSG Вимк., 1 FET, R41 1 кОм

*Рис. 8-5. DSG Вимк., 1 FET, R41 1 кОм*

Рис. 8-6. DSG Увімк., 2 FET, 10 кОм, 470 нФ

*Рис. 8-6. DSG Увімк., 2 FET, 10 кОм, 470 нФ*

Рис. 8-7. DSG Вимк., 2 FET, R41 1 кОм

*Рис. 8-7. DSG Вимк., 2 FET, R41 1 кОм*

Рис. 8-8. DSG Увімк., 4 FET, 10 кОм, 470 нФ

*Рис. 8-8. DSG Увімк., 4 FET, 10 кОм, 470 нФ*

Рис. 8-9. DSG Вимк., 4 FET, R41 1 кОм

*Рис. 8-9. DSG Вимк., 4 FET, R41 1 кОм*

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

Рис. 8-10. DSG Увімк., 8 FET, 10 кОм, 470 нФ

*Рис. 8-10. DSG Увімк., 8 FET, 10 кОм, 470 нФ*

Рис. 8-11. DSG Вимк., 8 FET, R41 1 кОм

*Рис. 8-11. DSG Вимк., 8 FET, R41 1 кОм*

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

Рис. 8-12. DSG Увімк., 8 FET, 10 кОм, 470 нФ

*Рис. 8-12. DSG Увімк., 8 FET, 10 кОм, 470 нФ*

Рис. 8-13. DSG Вимк., 8 FET, R41 100 Ом

*Рис. 8-13. DSG Вимк., 8 FET, R41 100 Ом*

Рис. 8-14. DSG Увімк., 12 FET, 10 кОм, 470 нФ

*Рис. 8-14. DSG Увімк., 12 FET, 10 кОм, 470 нФ*

Рис. 8-15. DSG Вимк., 12 FET, R41 100 Ом

*Рис. 8-15. DSG Вимк., 12 FET, R41 100 Ом*

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

**Таблиця 8-1. Часи спадання для різної кількості FET, 100 Ом**

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

Рис. 8-16. DSG Увімк., 12 FET, 10 кОм, PNP, 470 нФ

*Рис. 8-16. DSG Увімк., 12 FET, 10 кОм, PNP, 470 нФ*

Рис. 8-17. DSG Вимк., 12 FET, R41 1 кОм, PNP

*Рис. 8-17. DSG Вимк., 12 FET, R41 1 кОм, PNP*

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

Рис. 8-18. Управління DSG без схеми захисту від зворотної зарядки

*Рис. 8-18. Управління DSG без схеми захисту від зворотної зарядки*

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

*Рис. 8-19. DSG Увімк., 12 FET, 100 Ом, без схеми зворотного заряду, 470 нФ*

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

*Рис. 8-20. DSG Вимк., 12 FET, 100 Ом, без схеми зворотного заряду*

Якщо схема зворотного заряду потрібна, P-канальний FET може бути встановлений замість R45 з затвором, прив'язаним до виводу LD, як показано на Рис. 8-21. FET буде увімкненим, коли DSG піднімається; при падінні DSG до LD FET вимикається, і R40 допоможе розряджати затворну ємність FET розряду, але вимкнеться, дозволяючи резистору відтягування затвора R41 завершити вимкнення. На Рис. 8-22 та Рис. 8-23 R40 = 1 кОм. При вимкненому DSG P-канальний FET Q32 вимкнений, і зворотна напруга зарядки знизить сітку Dgate без потоку струму через R40. При ввімкненні R40 діятиме разом із затворною ємністю і може бути підібраний так, щоб Dgate краще відповідала виводу DSG. Пам'ятайте, що струм ввімкнення надходить від конденсатора CP1, і просідання DSG залежатиме від внутрішнього опору та передачі заряду від конденсатора CP1 до затворів FET. Цей приклад використовує конденсатор CP1 470 нФ, і знижену напругу після ввімкнення можна спостерігати. При вимкненні R40 паралельний шляху R41 та Шоттки до тих пір, поки напруга не стане достатньо низькою для вимкнення P-канального FET. Слід зазначити, що BQ7694204 не обмежує напругу між DSG та LD при ввімкненні. Мета P-канальної схеми — дозволити використання малого R40, щоб затвори FET, PACK+ та LD швидко піднімалися разом з DSG. Якщо використовується великий R40, або ввімкнення FET розряду є повільним, бажаний стабілітрон на з'єднанні джерело-затвор і великий резистор від затвора Q32 до з'єднання LD для захисту затвора Q32.

Рис. 8-21. Схема ввімкнення DSG P-ch

*Рис. 8-21. Схема ввімкнення DSG P-ch*

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

*Рис. 8-22. DSG Увімк., 12 FET, P-ch, шлях ввімкнення 1 кОм, 470 нФ*

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

*Рис. 8-23. DSG Вимк., 12 FET, P-ch, шлях ввімкнення 1 кОм, 100 Ом*

Приклад короткого замикання показано на Рис. 8-24 з одним FET і кількома кОм для R41. При виникненні короткого замикання BAT+ та PACK+ утримуються разом FET та притягуються вниз навантаженням. Розряд виводу BAT блокується конденсатором виводу BAT, а конденсатор CP1 утримує напругу зарядового насоса вище нього як джерело живлення для виходів CHG та DSG. Затвори FET заряду та розряду захищені D1 та D2 у Рис. 5-1. CHG та DSG завантажуються і дещо просідають через їх внутрішній опір, але більша частина напруги падає на резистори до затворів: R44, R40 та R45. Напруга DSG впаде, оскільки подія короткого замикання вимірюється за часом. При більших затримках SCD та менших резисторах затворів CHG та DSG впадуть до тих пір, поки D1 та D2 не перестануть проводити. BQ7694204 відраховує час події за допомогою джерела живлення REG18. Коли вибрана затримка спрацьовує, DSG вимикається, як описано раніше. R41 вимикає FET розряду і має бути вибраний таким чином, щоб вимикати FET достатньо швидко для уникнення надмірного нагрівання і достатньо повільно для уникнення надмірного підвищення BAT+.

Рис. 8-24. Приклад короткого замикання

*Рис. 8-24. Приклад короткого замикання*

---

## 9 Шляхи струму драйвера DSG

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

Читач повинен зауважити, що якщо FET заряду Q2 вимкнений — як, наприклад, при перебуванні BQ7694204 у режимі SLEEP через відсутність навантажувального струму, — R26 підніме напругу PACK+ приблизно до напруги зарядового насоса. Таким чином, незавантажений акумуляторний блок із BQ7694204 у режимі SLEEP може показати напругу PACK+ вище напруги батареї.

Рис. 9-1. Шлях струму ввімкнення DSG

*Рис. 9-1. Шлях струму ввімкнення DSG*

Типовий рекомендований резистор затвор-джерело (R26) становить 10 МОм, забезпечуючи навантаження приблизно 1,1 мкА при роботі зарядового насоса на рівні $V_{(FETON\_HI)}$. Хоча будь-яке навантаження спричинить деяке просідання напруги зарядового насоса, зарядовий насос зазвичай може підтримувати 10 В при навантаженні на драйвери приблизно до 40 мкА. Зарядовий насос спільний із драйвером CHG, тому його навантаження також слід враховувати. При завантаженні драйвера DSG його напруга впаде, що також призведе до падіння напруги на виводі CHG, якщо CHG також увімкнений. Зарядовий насос може подавати приблизно 200 мкА у заземлений резистор затвор-джерело при напрузі BAT+. Однак при заземленому резисторі затвор-джерело FET розряду буде вимкнений, і напруга PACK+ швидше за все впаде через навантаження. При відтягуванні DSG нижче рівня BAT+ додатковий струм потече через вивід DSG від виводу BAT. Цей струм є обмеженим; приклад показано на Рис. 9-2. При реалізації схеми для перевизначення виводу DSG слід передбачити деякий запас вище обмеження струму, щоб переконатись, що FET розряду вимкнений і не працює як повторювач джерела. Також враховуйте відтягування CHG: знижена напруга залишить FET заряду вимкненим. Може бути корисним сигналізувати вимкнення виходу CHG FET через вхід CFETOFF мікросхеми BQ7694204, де це доступно.

Рис. 9-2. DSG під навантаженням при батареї 36 В

*Рис. 9-2. DSG під навантаженням при батареї 36 В*

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

Рис. 9-3. Шлях струму вимикання DSG

*Рис. 9-3. Шлях струму вимикання DSG*

---

## 10 Висновок

Пристрої сімейства BQ7694204 забезпечують управління FET з боку високої напруги і можуть використовуватися в конфігураціях з кількома FET. Розміряйте конденсатор CP1 для допустимого просідання при ввімкненні FET. Вибирайте резистори у з'єднаннях виводів CHG та DSG до затвора для відповідного ввімкнення та вимкнення FET. За необхідності передбачайте допоміжні схеми вимкнення або ввімкнення, що відповідають вимогам прикладної системи. Схеми та результати тестів, представлені в цьому документі, допоможуть розробнику розпізнати умови для розгляду у своїй конструкції. Зверніться до паспортів даних та технічних довідкових посібників для отримання інформації про пристрій та конфігурацію.

---

## 11 Посилання

- Texas Instruments, *BQ7694204 3S-16S Battery Monitor and Protector Data Sheet*
- Texas Instruments, *BQ769142 3S-14S Battery Monitor and Protector Data Sheet*
- Texas Instruments, *BQ76942 3S-10S Battery Monitor and Protector Data Sheet*
- Texas Instruments, *BQ7694204 Technical Reference Manual*
- Texas Instruments, *BQ769142 Technical Reference Manual*
- Texas Instruments, *BQ76942 Technical Reference Manual*
- Texas Instruments, *BQ7694204EVM User's Guide*
- Texas Instruments, *BQ76942EVM User's Guide*
- Texas Instruments, *CSD19536KCS 100-V, N-Channel NexFET™ Power MOSFET*

---

## 12 Історія ревізій

*Примітка: Номери сторінок у попередніх ревізіях можуть відрізнятися від номерів сторінок у поточній версії.*

**Зміни від Ревізії \* (Вересень 2020) до Ревізії A (Березень 2022)**

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
