LVladymyr/WAFEL-Evaluation-Board/Documents/Assets/Pasted image 20260329170259.png

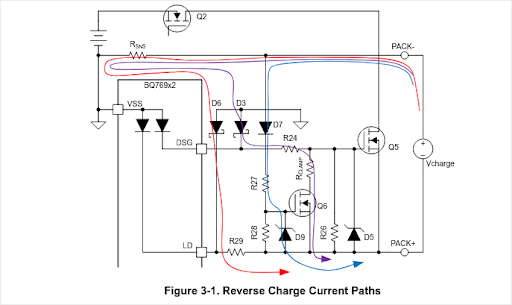
Documents/Assets/Pasted image 20260329170259.png
