LVladymyr/WAFEL-Evaluation-Board/Documents/Assets/Pasted image 20260402193022.png

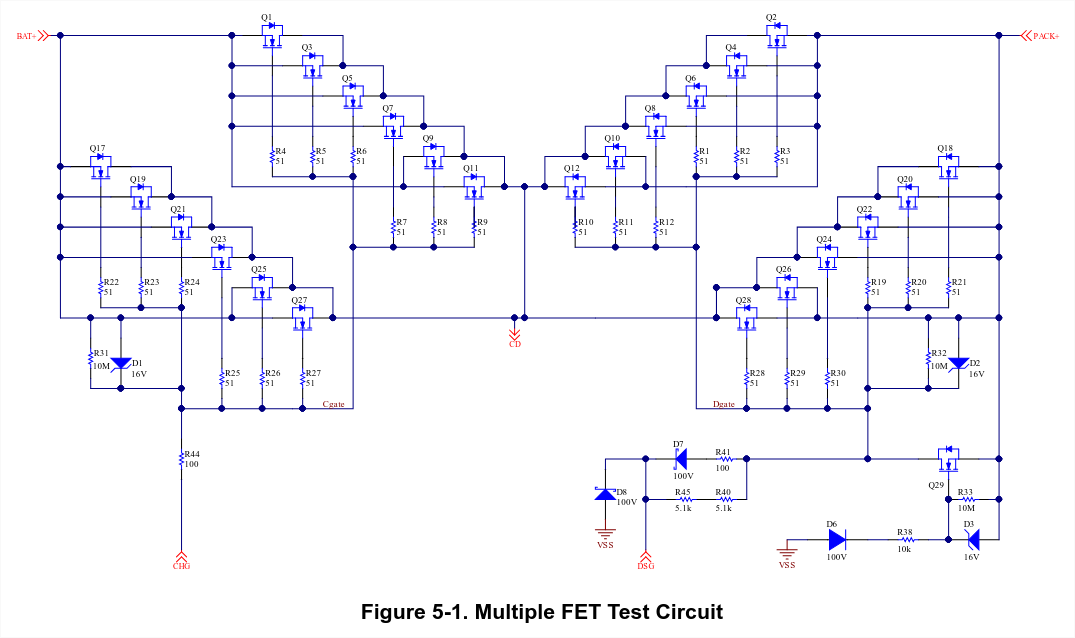
Documents/Assets/Pasted image 20260402193022.png
