LVladymyr/WAFEL-Evaluation-Board/Documents/Assets/Pasted image 20260403140523.png

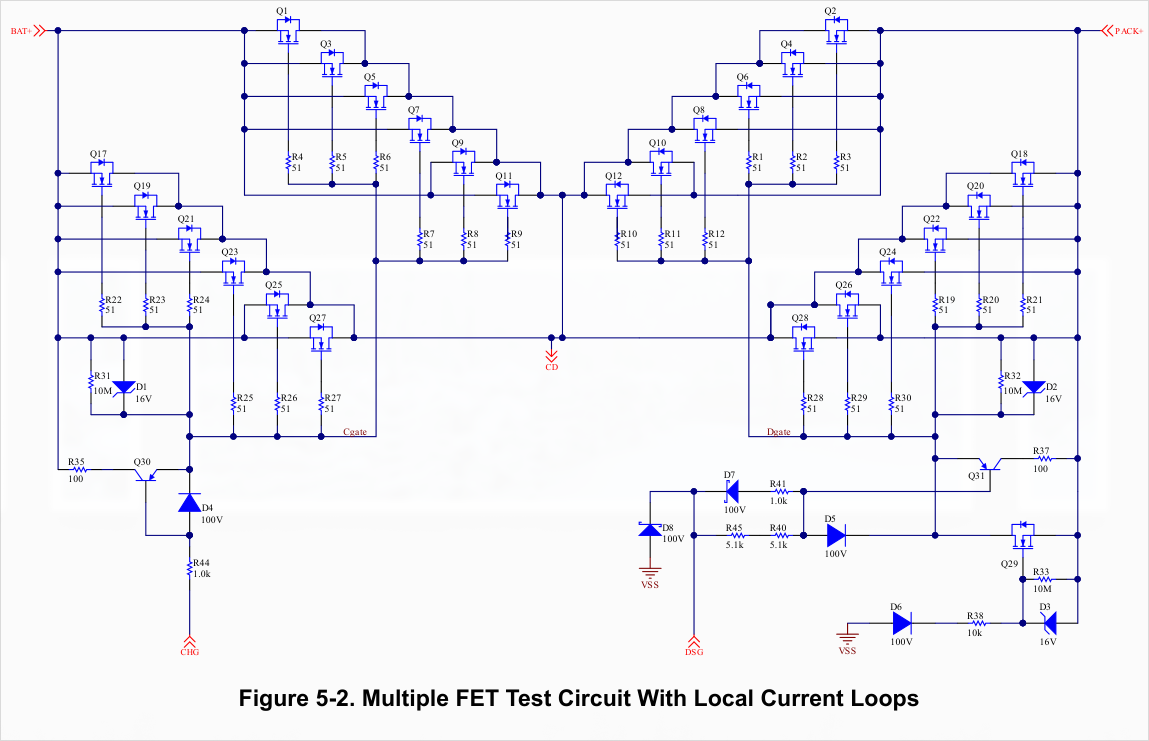
Documents/Assets/Pasted image 20260403140523.png
