LVladymyr/WAFEL-Evaluation-Board/Documents/Assets/Pasted image 20260403140707.png

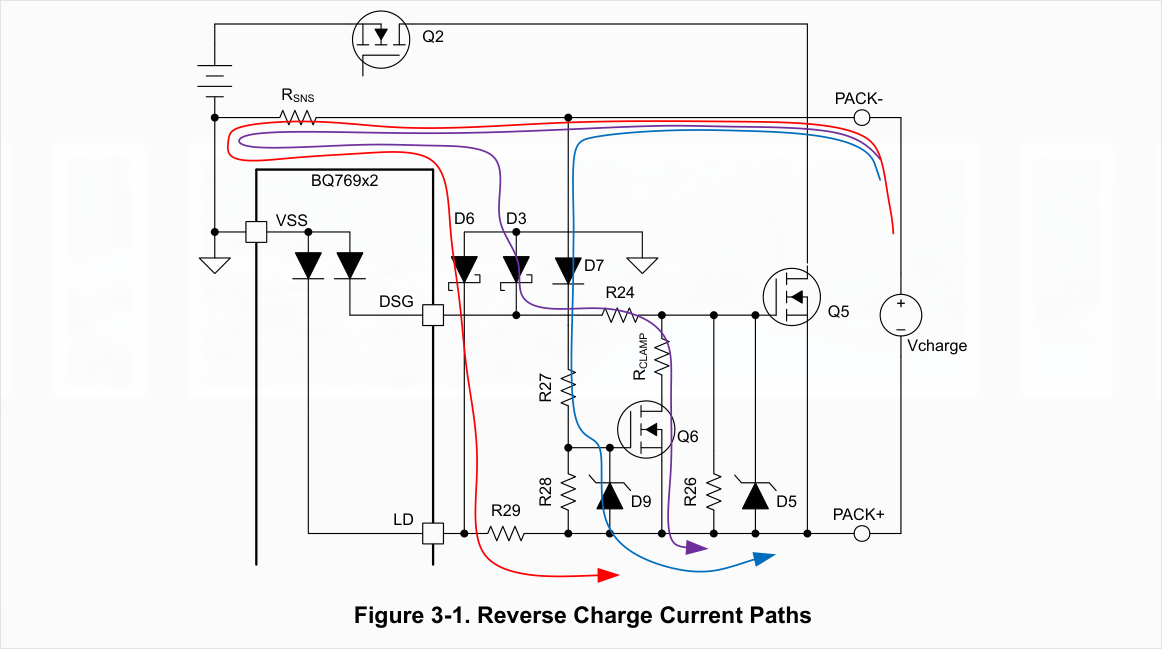
Documents/Assets/Pasted image 20260403140707.png
