LVladymyr/WAFEL-Evaluation-Board/Documents/Assets/Pasted image 20260403155612.png

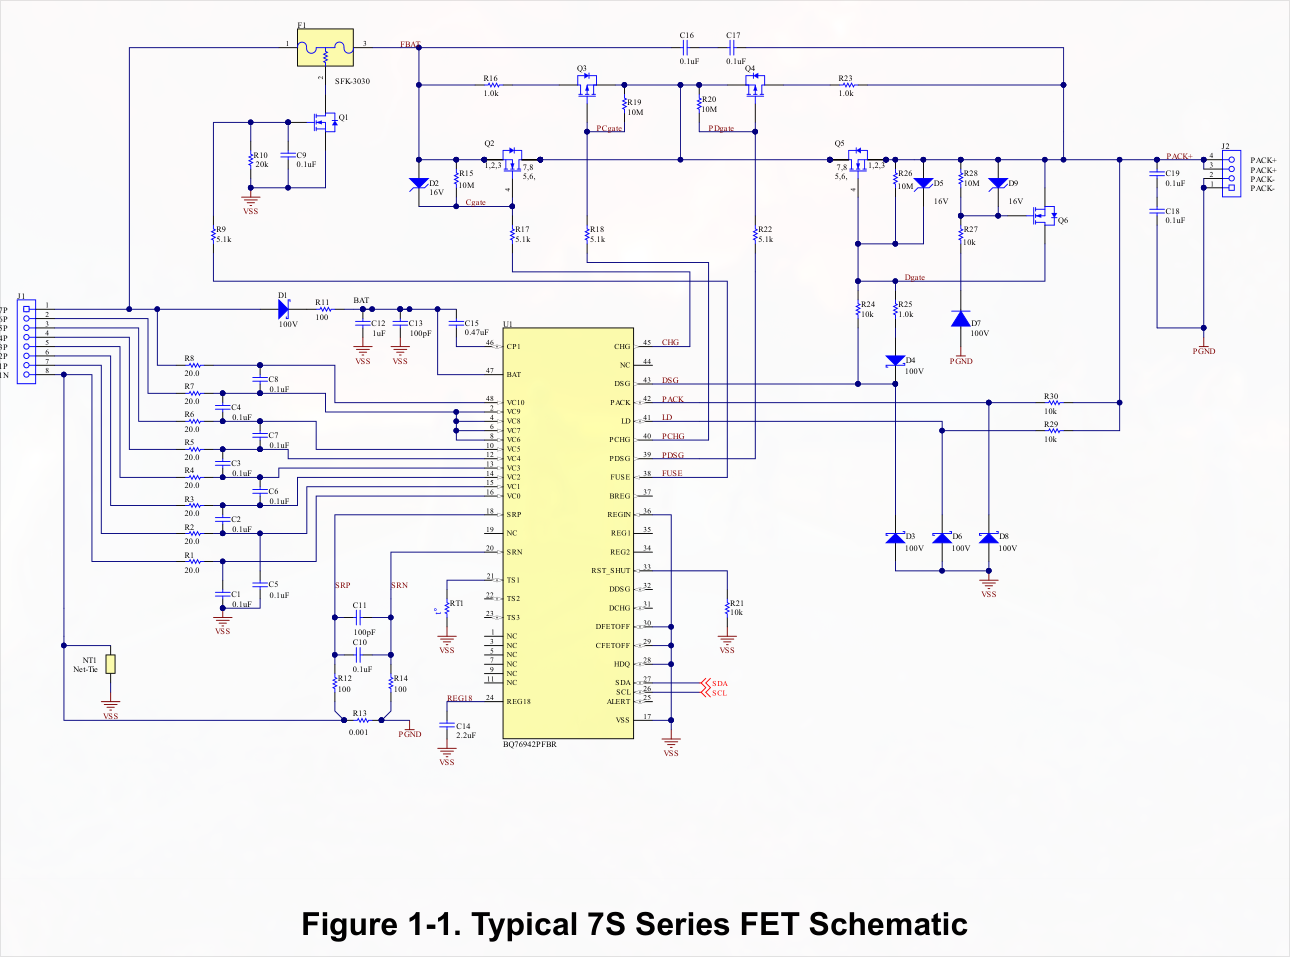
Documents/Assets/Pasted image 20260403155612.png
