LVladymyr/WAFEL-Evaluation-Board/itv_page1-1.png

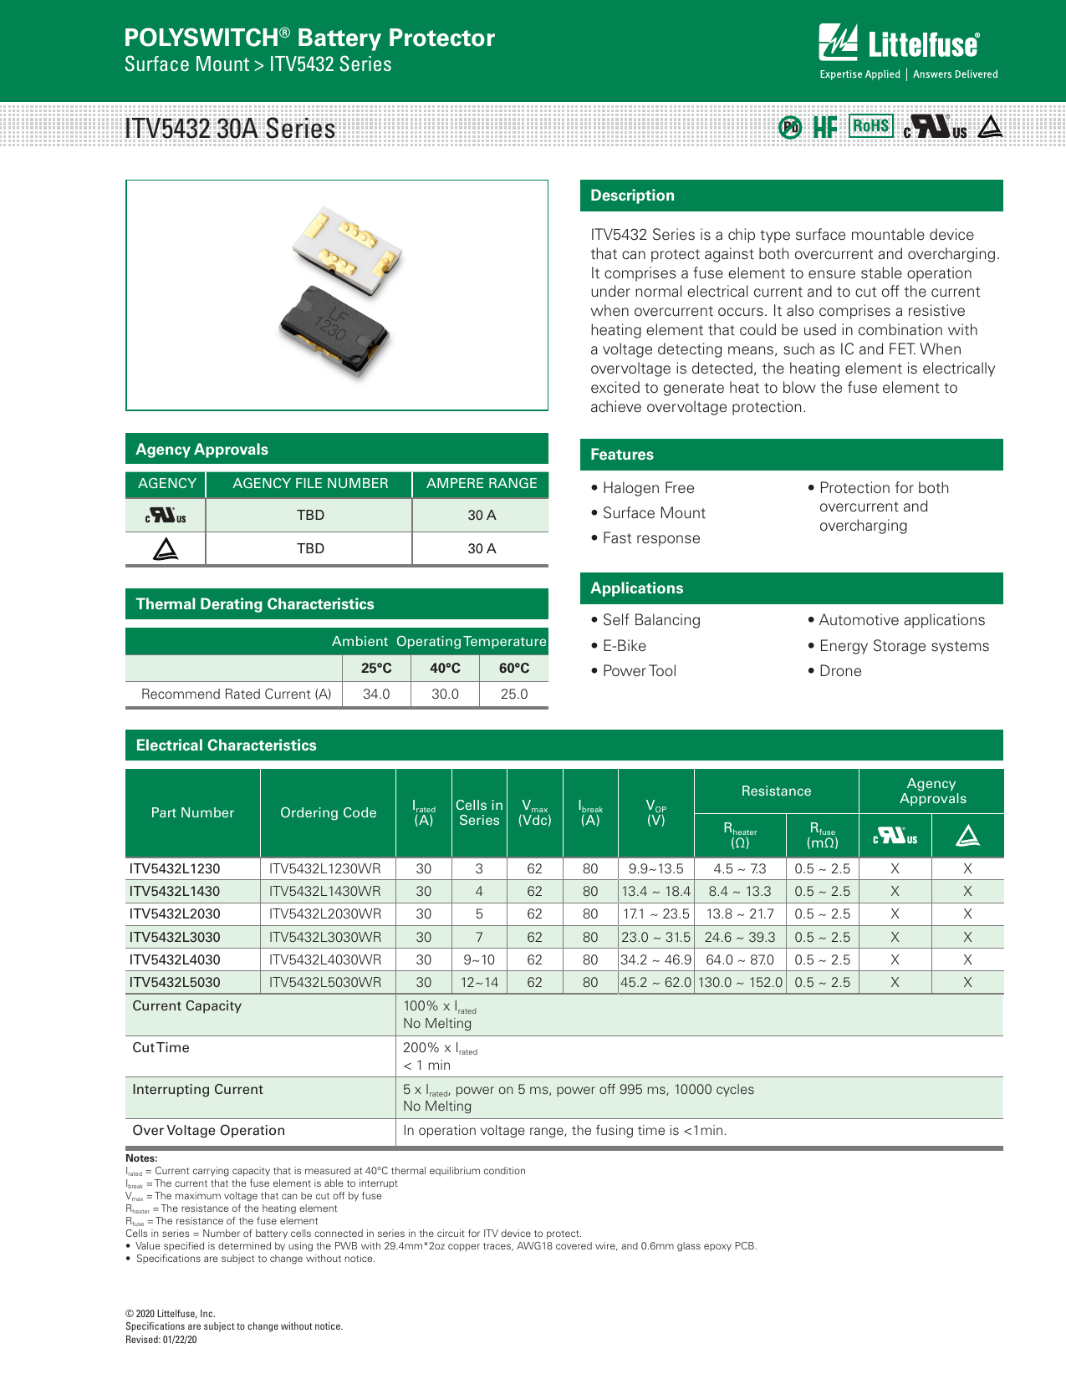
itv_page1-1.png
